IRNAS/smartparks-rhino-tracker-hardware/02_MCU/04_OUTPUT_FILES/Rhino_V2_P1.png

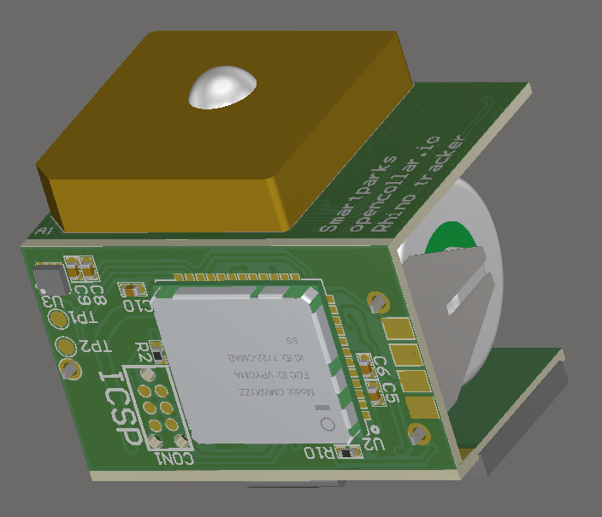
02_MCU/04_OUTPUT_FILES/Rhino_V2_P1.png
