IRNAS/smartparks-rhino-tracker-hardware/11_DOC/Rhino Tracker 3.png

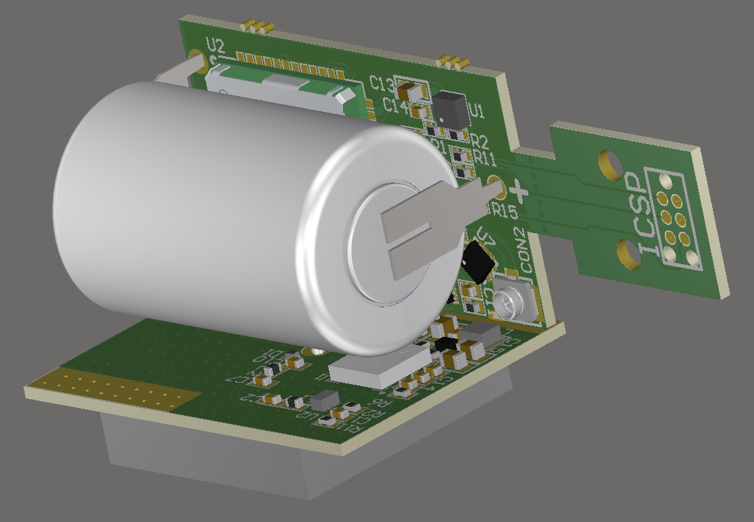
11_DOC/Rhino Tracker 3.png
