IRNAS/smartparks-rhino-tracker-hardware/11_DOC/Rhino_V2_1_3.png

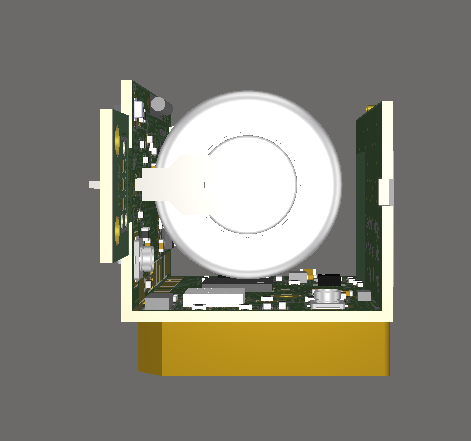
11_DOC/Rhino_V2_1_3.png
