IRNAS/smartparks-rhino-tracker-hardware/02_MCU/06_RELEASE/V2.4/Rhino - MCU_V2.4_3D/Rhino - MCU_V2.4_PCB_3D_PRINT.pdf

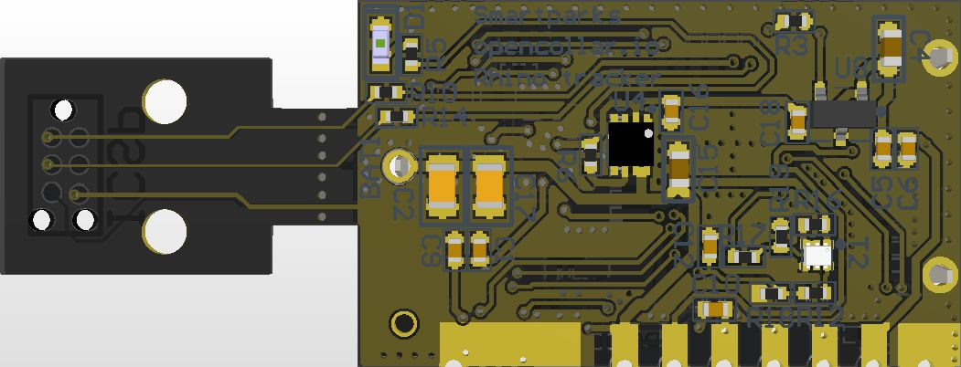
[picture p31: figure]

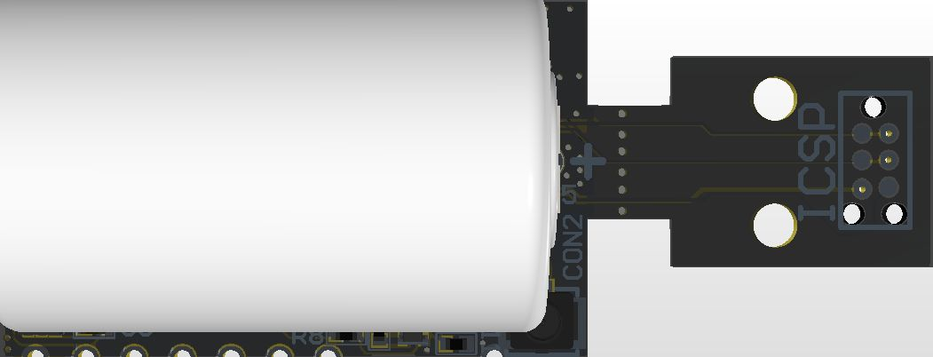
[picture p32: figure]
