IRNAS/smartparks-rhino-tracker-hardware/01_GPS/06_RELEASE/V2.2/Rhino - GPS_V2.2_3D/Rhino - GPS_V2.2_PCB 3D Print.pdf

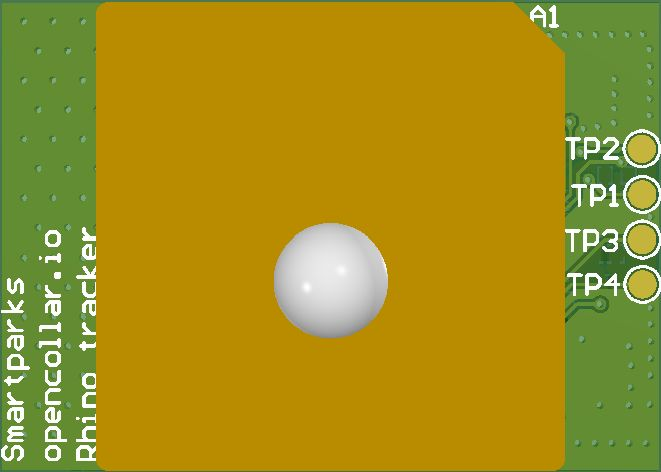
[picture p33: figure]

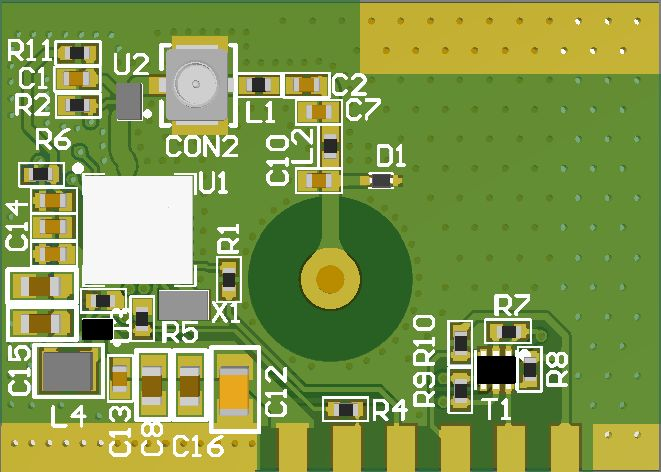
[picture p34: figure]
