IRNAS/smartparks-rhino-tracker-hardware/02_MCU/06_RELEASE/V2.2/Rhino - MCU_V2.2_3D/Rhino - MCU_V2.2_PCB_3D_PRINT.pdf

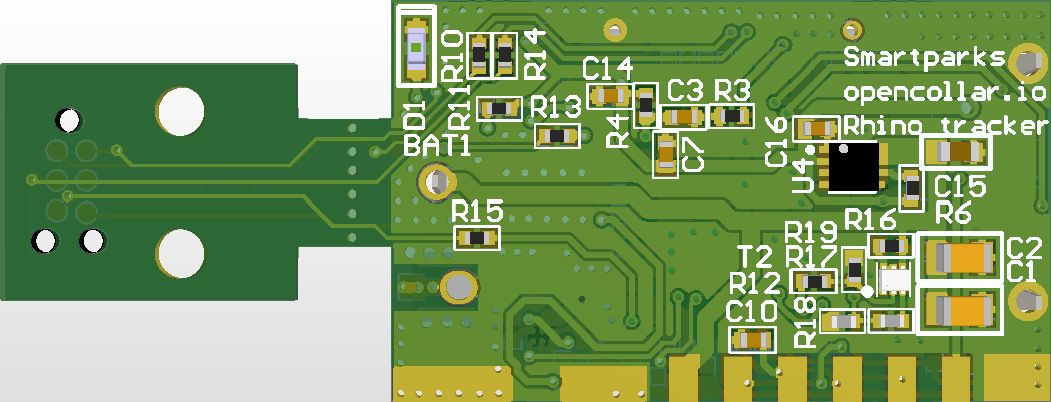
[picture p35: figure]

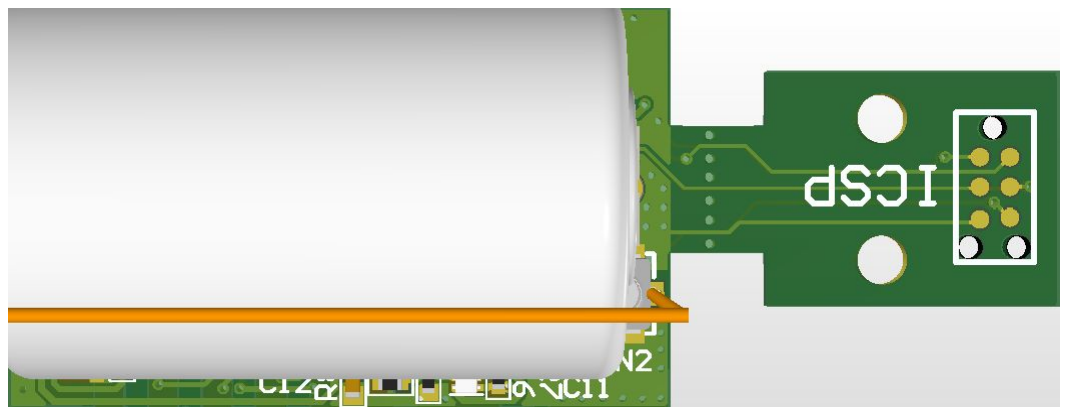
[picture p36: figure]
