IRNAS/smartparks-rhino-tracker-hardware/02_MCU/06_RELEASE/V2.4/Rhino - MCU_V2.4_SCHEMATICS/Rhino - MCU_V2.4_SCHEMATICS.PDF

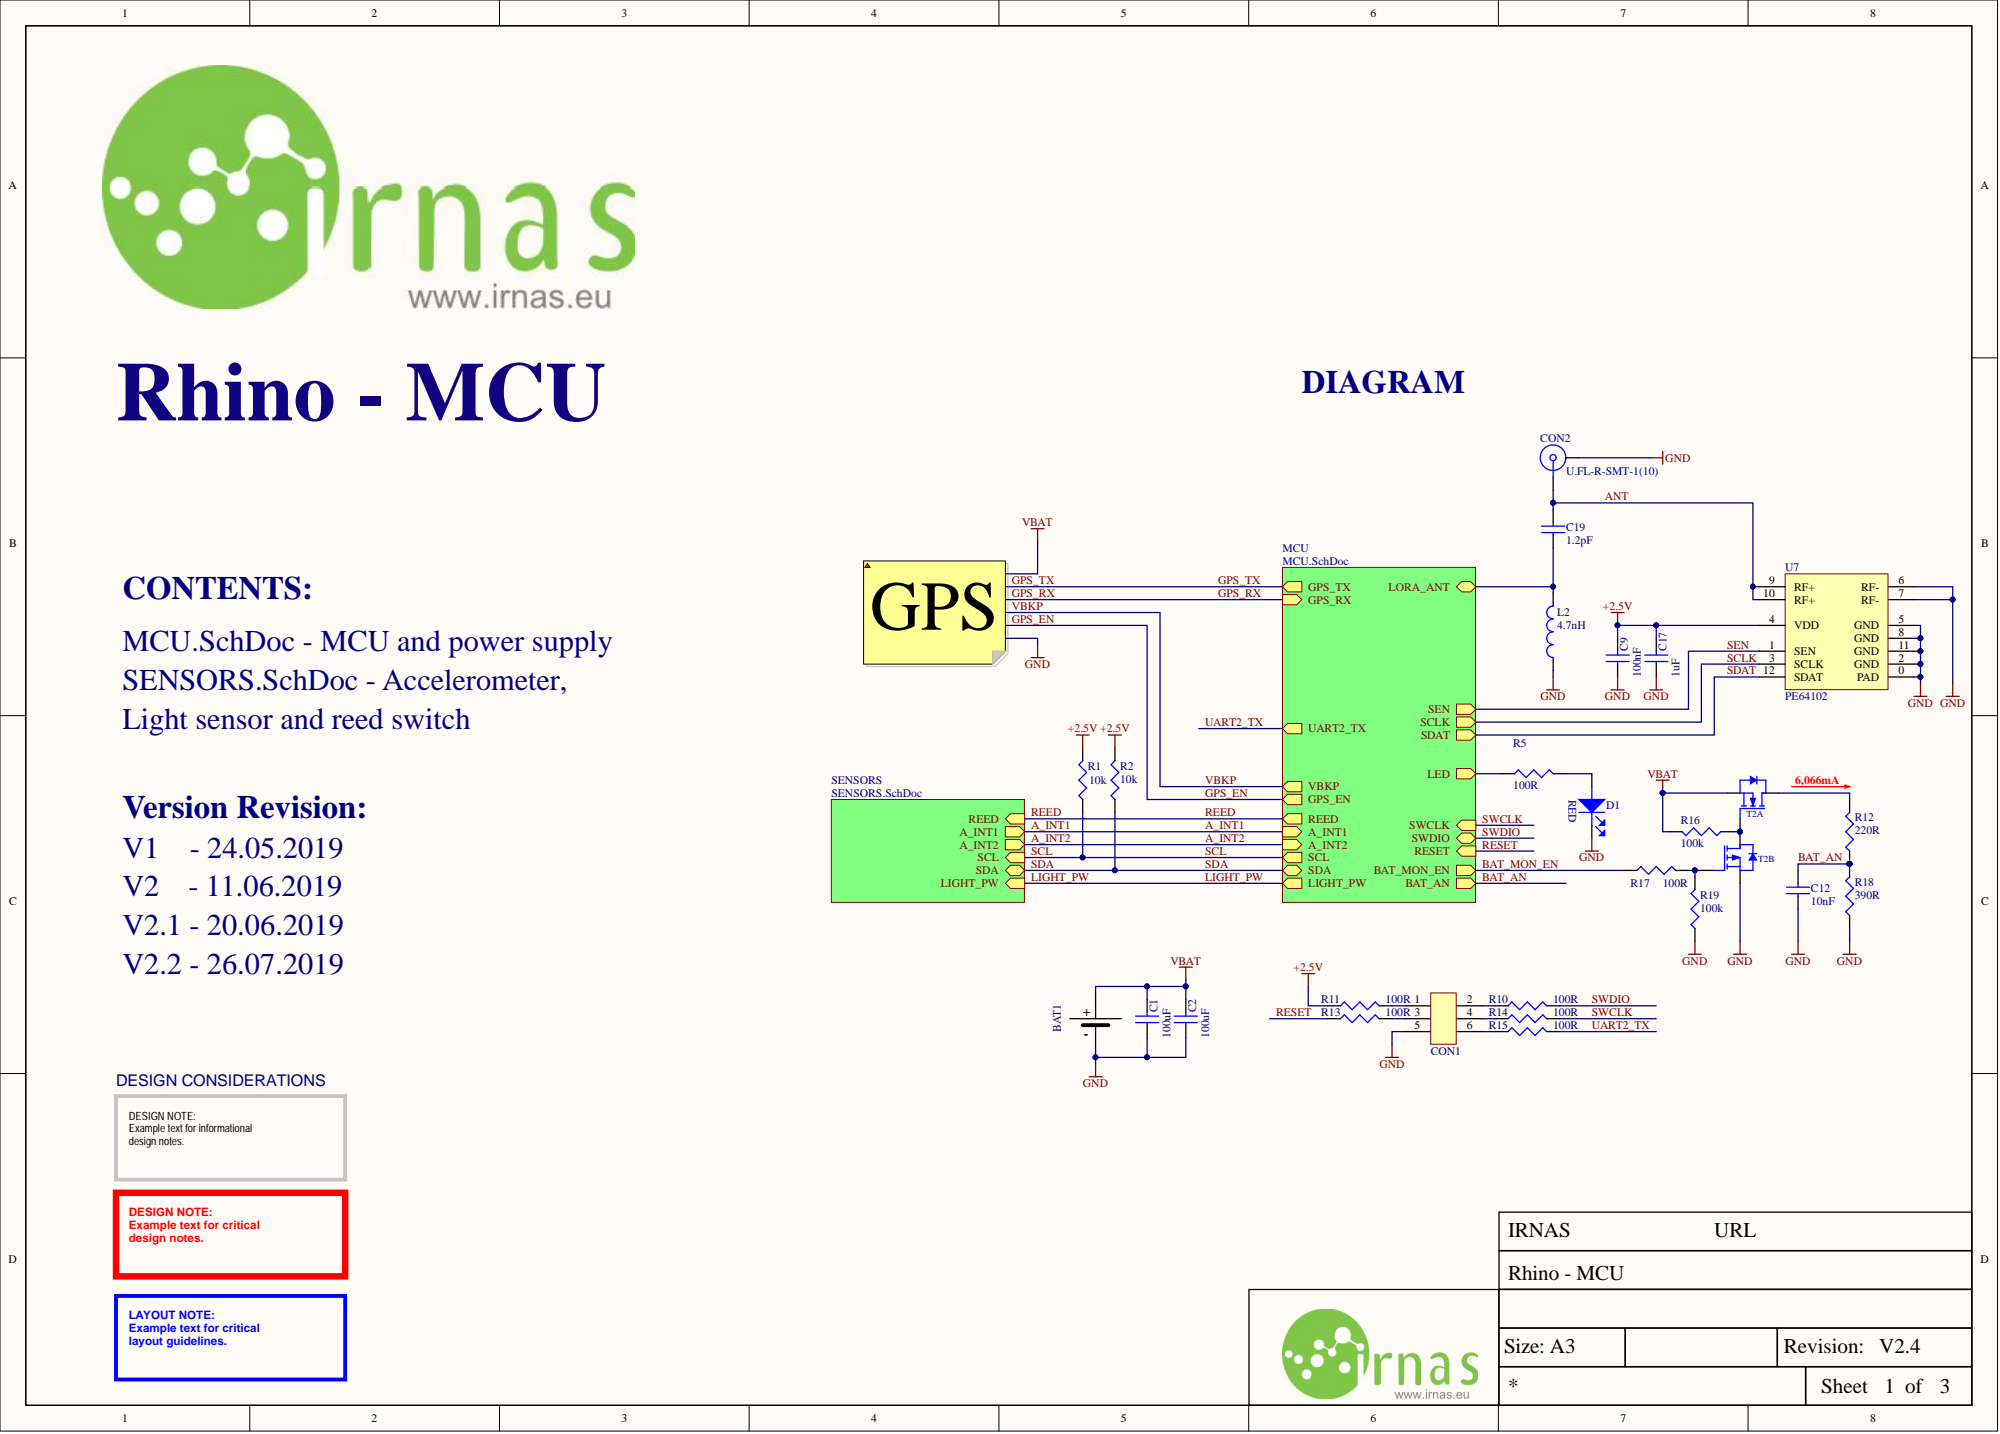
[picture p74: page 1]

MCU.SchDoc - MCU and power supply
SENSORS.SchDoc - Accelerometer,
Light sensor and reed switch

REED A_INT1 A_INT2 SCL SDA LIGHT_PW | REED | REED

A_INT1 | A_INT1
A_INT2 | A_INT2
SCL | SCL
SDA | SDA

DESIGN NOTE:
Example text for informational
design notes.

Example text for critical

LAYOUT NOTE:
layout guidelines.

Size: A3 | | Revision: V2.4

* | Sheet 1 of 3

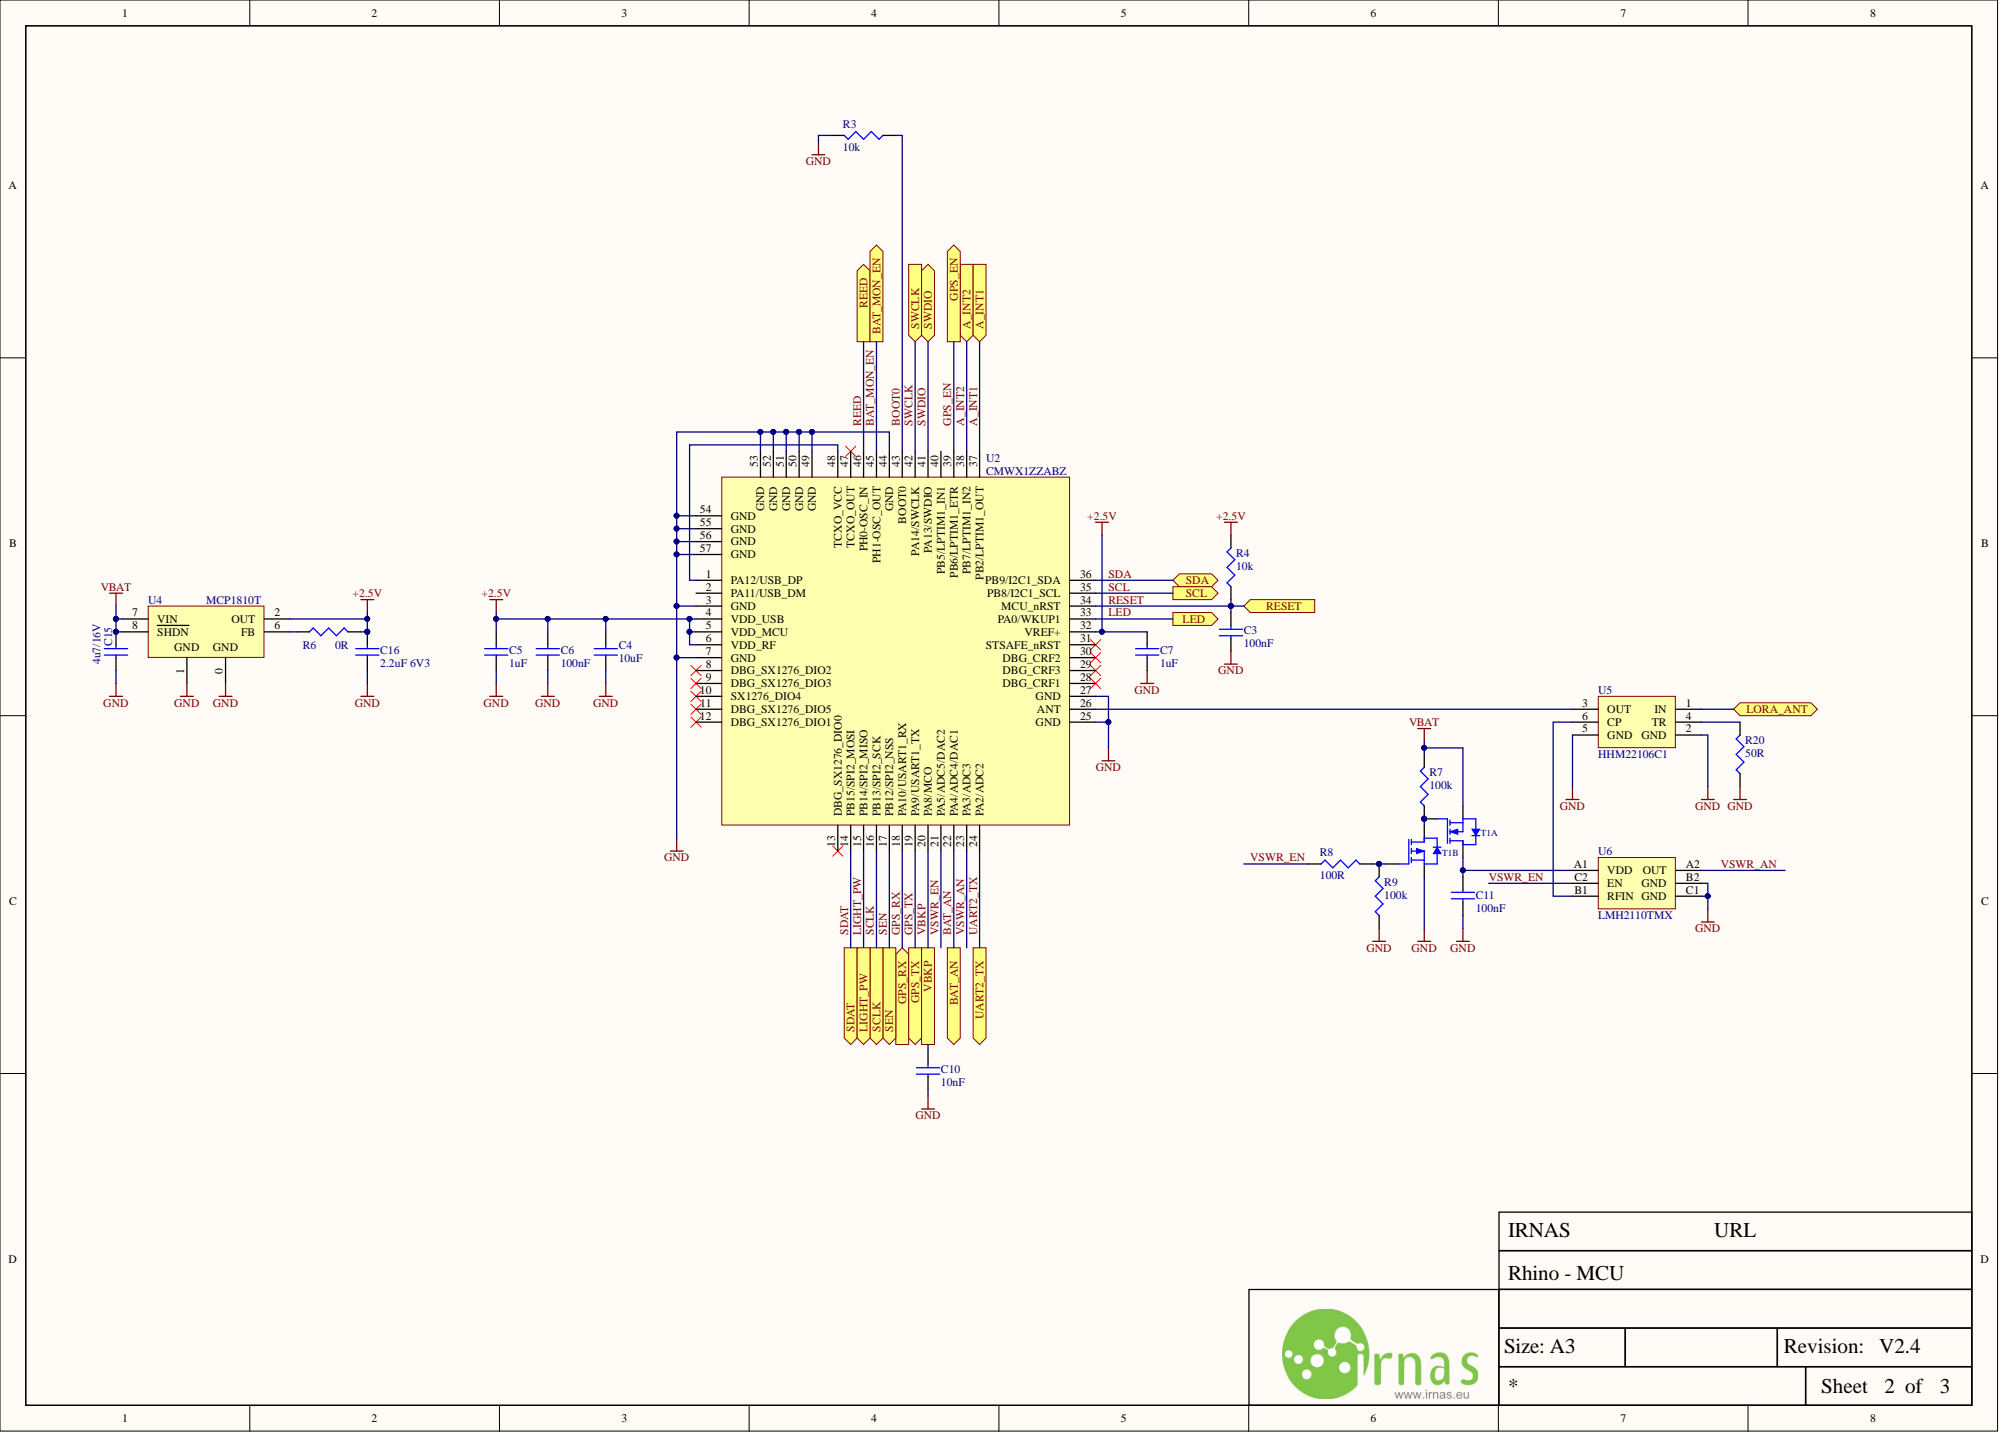
[picture p75: page 2]

GND 50 GND 51 GND 52 GND 53

OUT 37 PB7/LPTIM1_IN2 38 PB6/LPTIM1_ETR 39 PB5/LPTIM1_IN1 40 PA13/SWDIO 41 PA14/SWCLK 42 BOOT0 43 GND 44 PH1-OSC_OUT 45 PH0-OSC_IN 46 TCXO_OUT 47 TCXO_VCC 48

GND 54 | PA0/WKUP1 | 33 MCU_nRST 34 PB8/I2C1_SCL 35 PB9/I2C1_SDA
GND 55
GND 56
GND 57

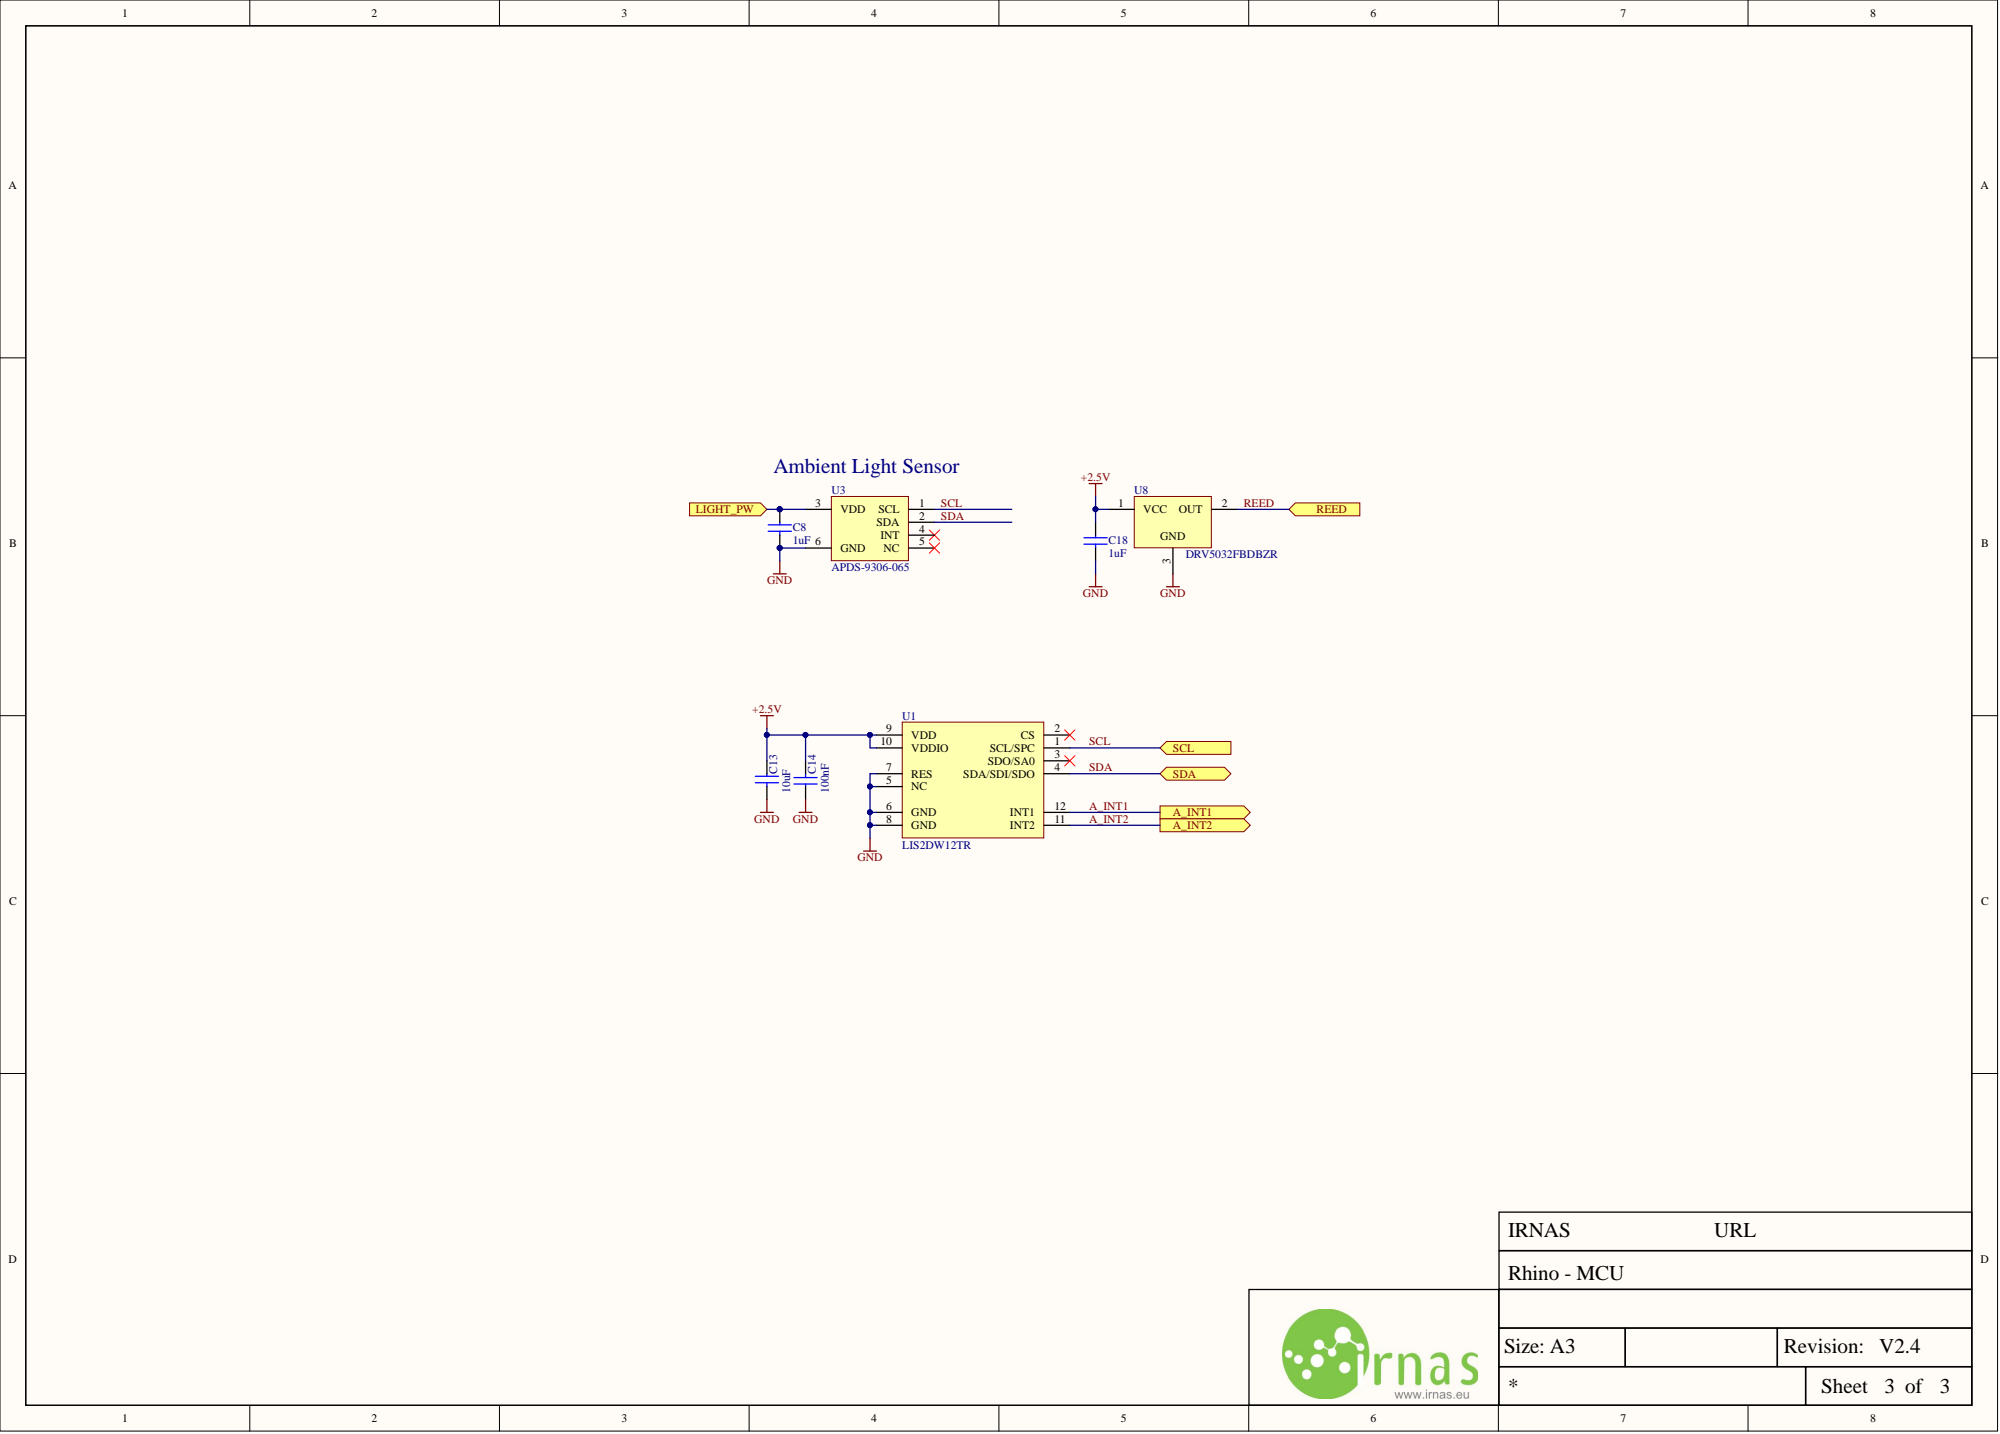
[picture p76: page 3]
