IRNAS/smartparks-rhino-tracker-hardware/01_GPS/06_RELEASE/V2.4/Rhino - GPS_V2.4_Assembly/Rhino - GPS_V2.4_Assembly.PDF

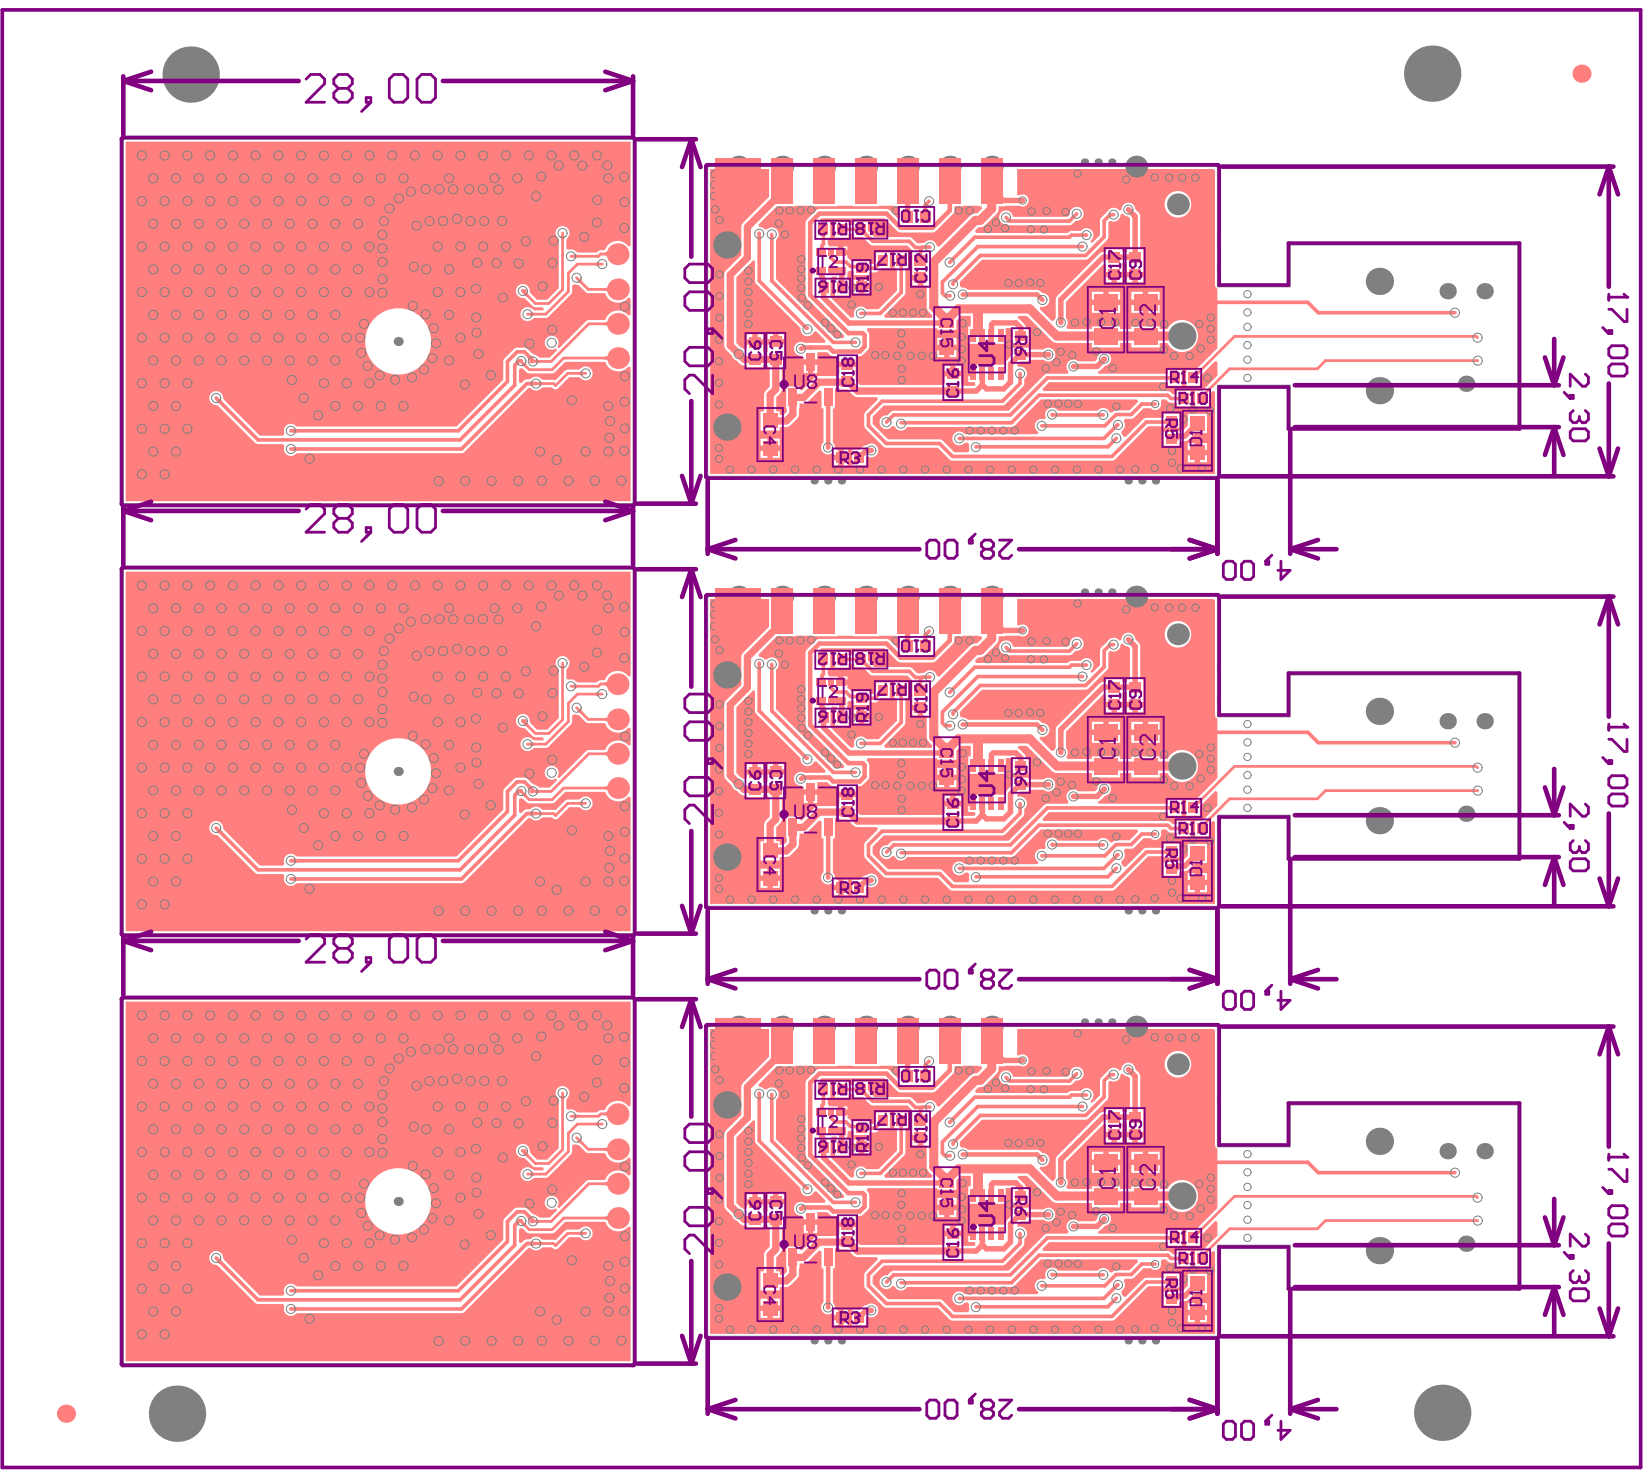
[picture p77: page 1]

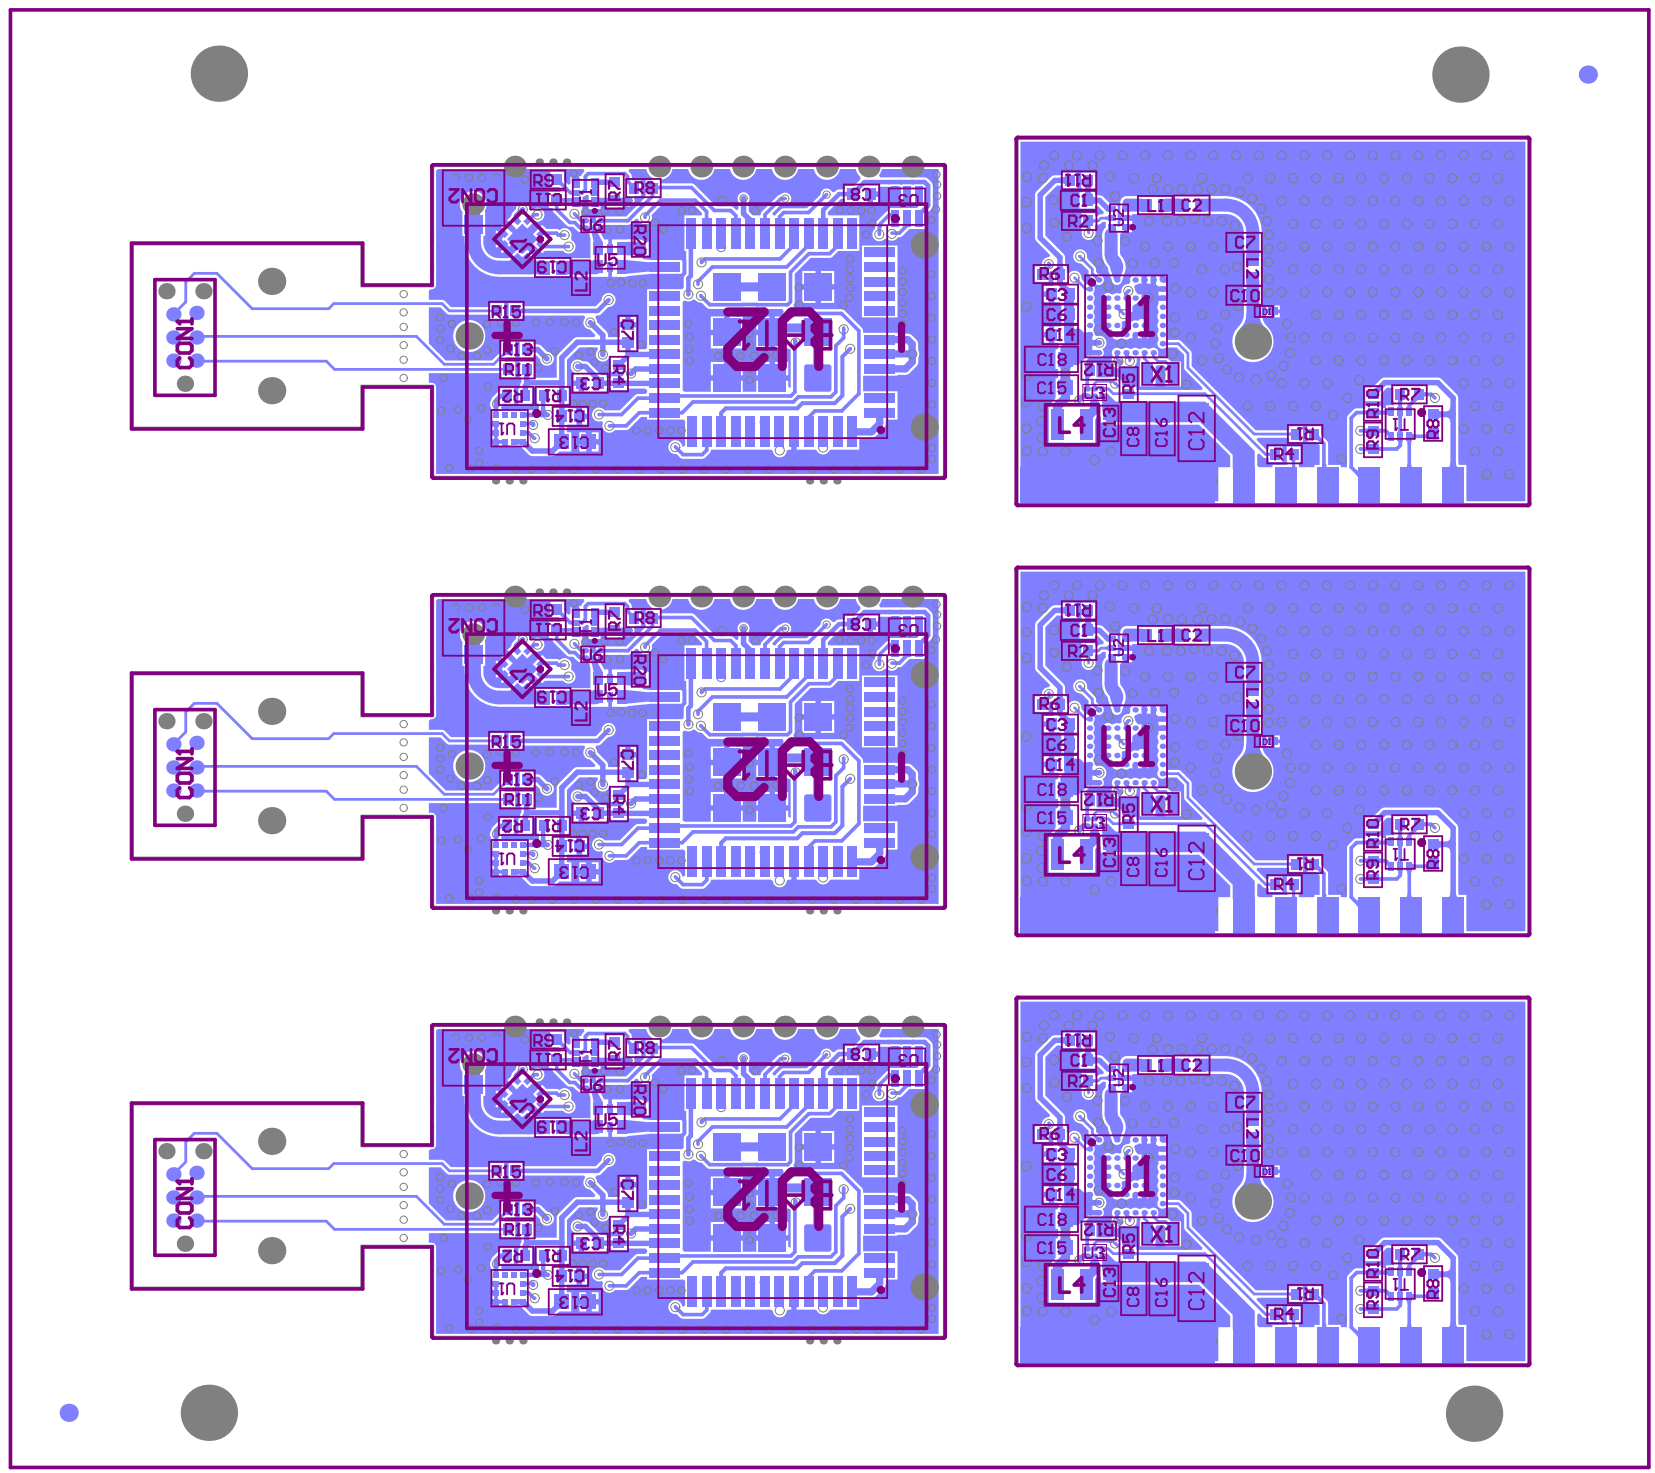
[picture p78: page 2]
