IRNAS/smartparks-rhino-tracker-hardware/01_GPS/06_RELEASE/V2.4/Rhino - GPS_V2.4_PCB_Print/Rhino - GPS_V2.4_PCB_Print.PDF

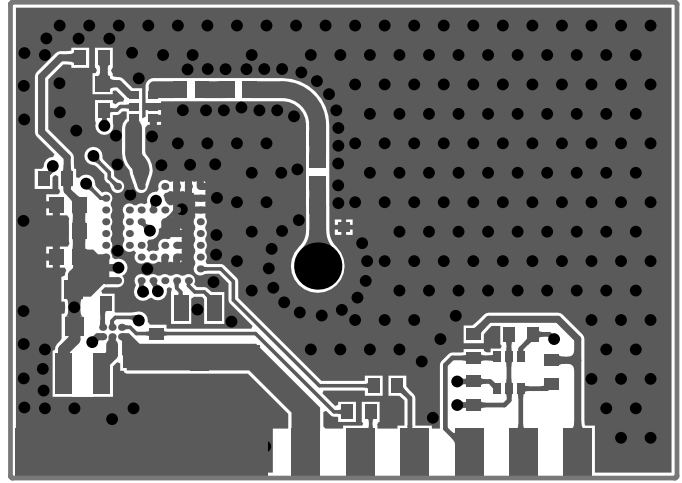
[picture p79: page 4]

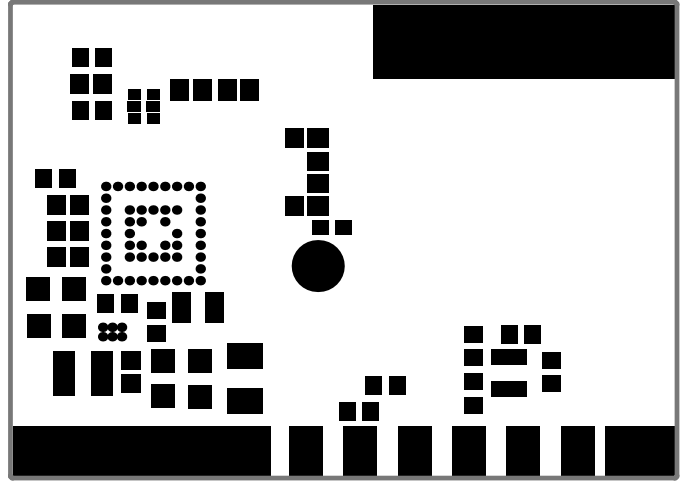
[picture p80: page 5]
