IRNAS/smartparks-rhino-tracker-hardware/02_MCU/06_RELEASE/V2.4/Rhino - MCU_V2.4_PCB_PRINT/Rhino - MCU_V2.4_PCB_PRINT.PDF

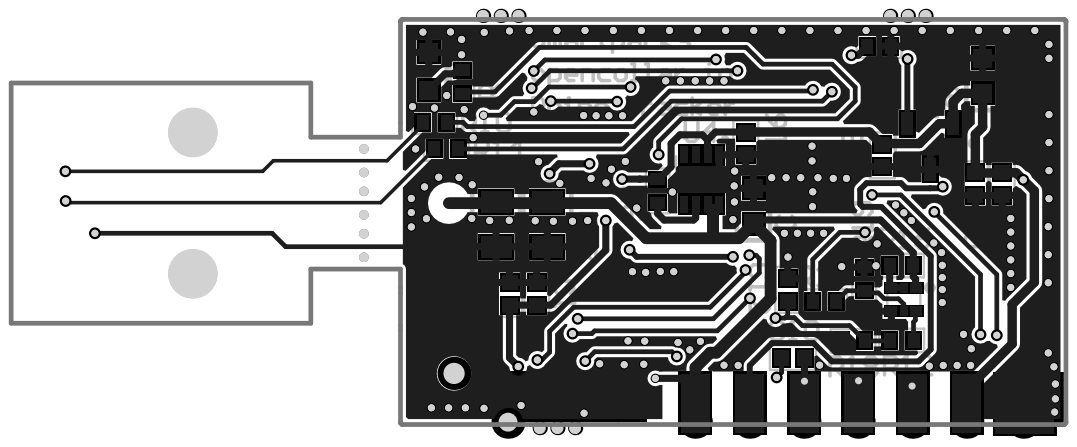
[picture p84: page 1]



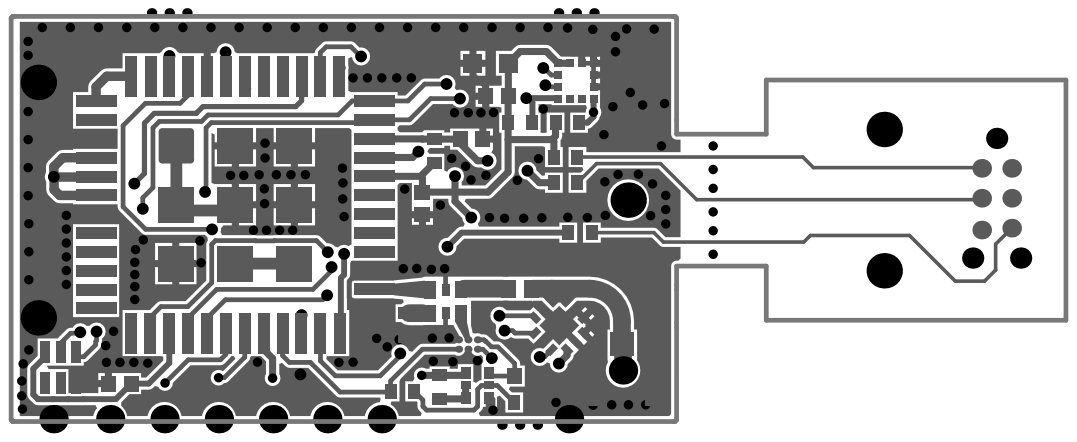
[picture p85: page 4]

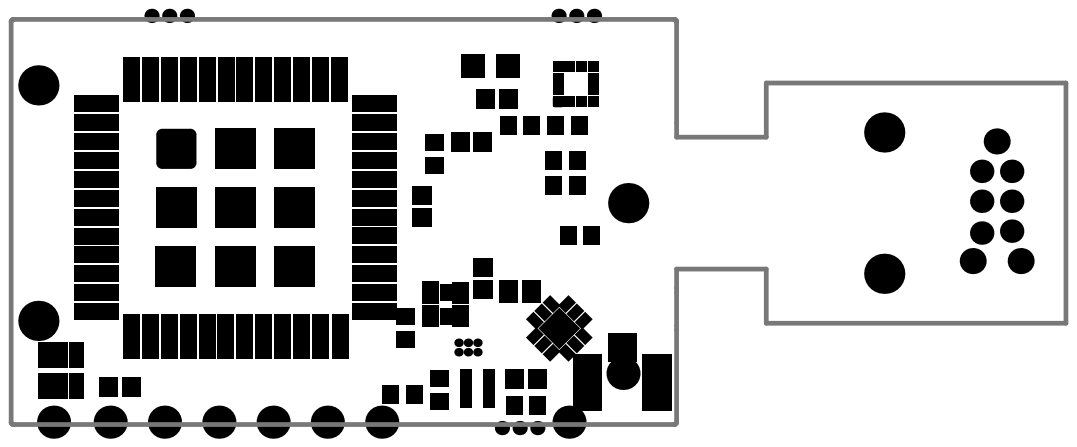
[picture p86: page 5]

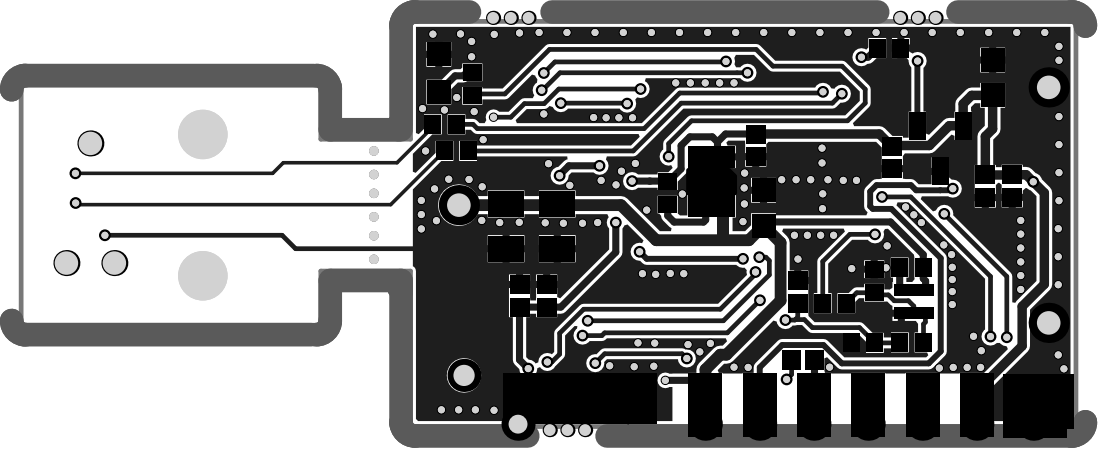
[picture p87: page 6]

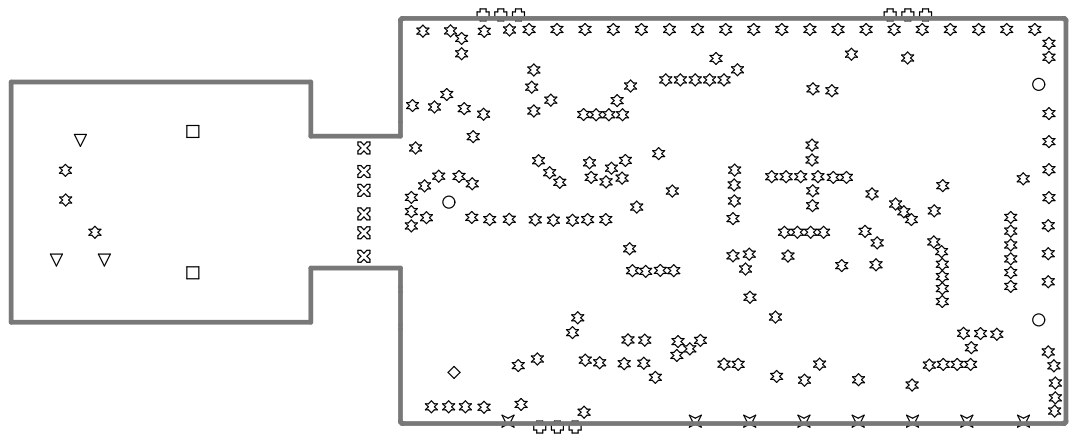
[picture p88: page 7]
