IRNAS/smartparks-rhino-tracker-hardware/01_GPS/06_RELEASE/V2.2/Rhino - GPS_V2.2_Assembly/Rhino - GPS_V2.2_Assembly.PDF

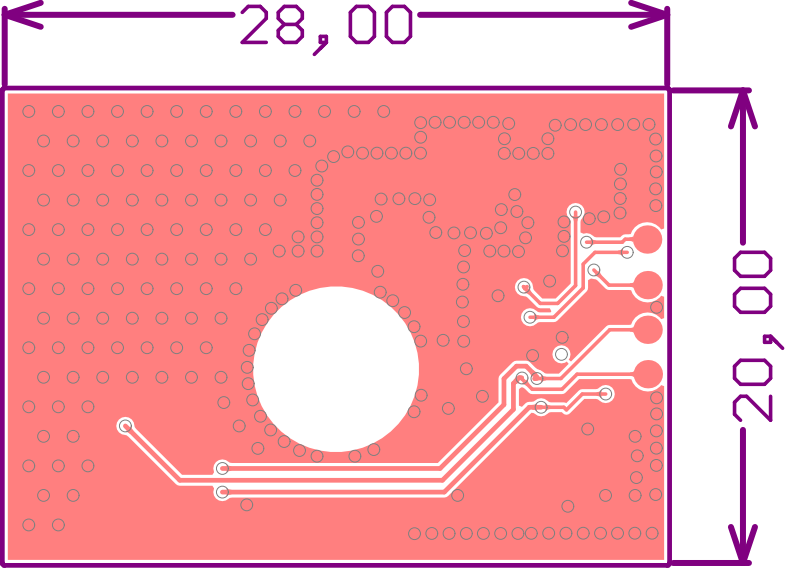
[picture p89: page 1]

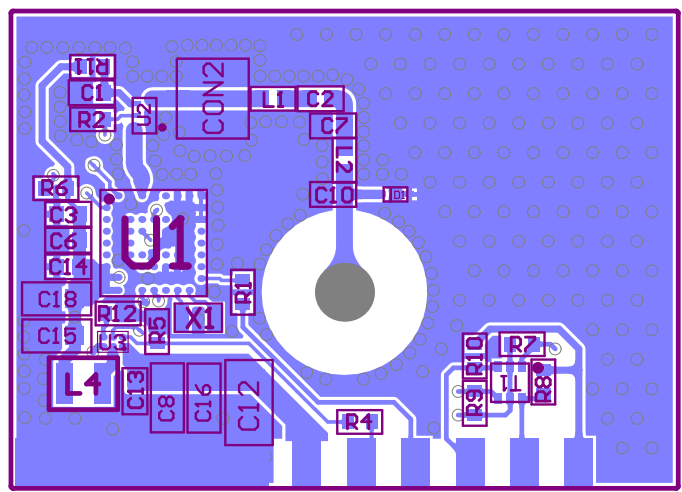
[picture p90: page 2]
