IRNAS/smartparks-rhino-tracker-hardware/01_GPS/06_RELEASE/V2.2/Rhino - GPS_V2.2_PCB_Print/Rhino - GPS_V2.2_PCB_Print.PDF

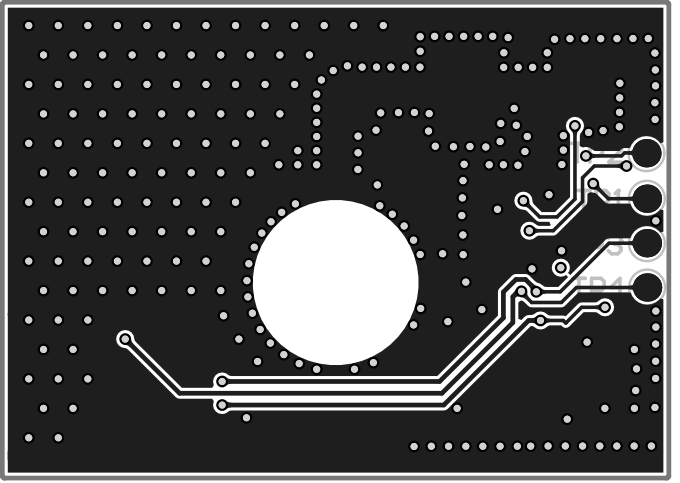
[picture p91: page 1]



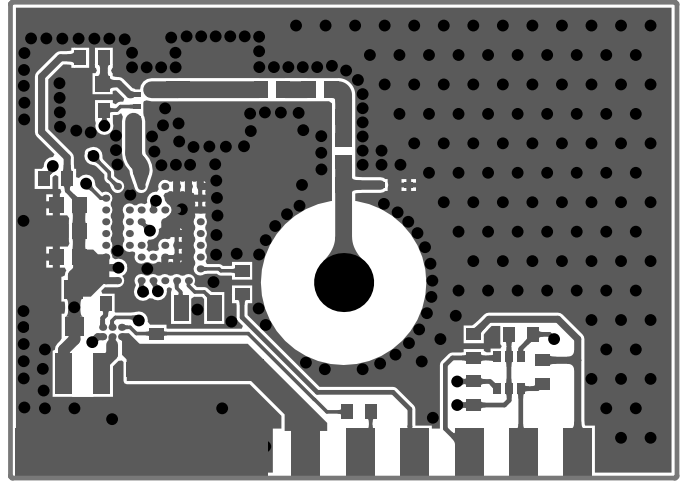
[picture p92: page 4]

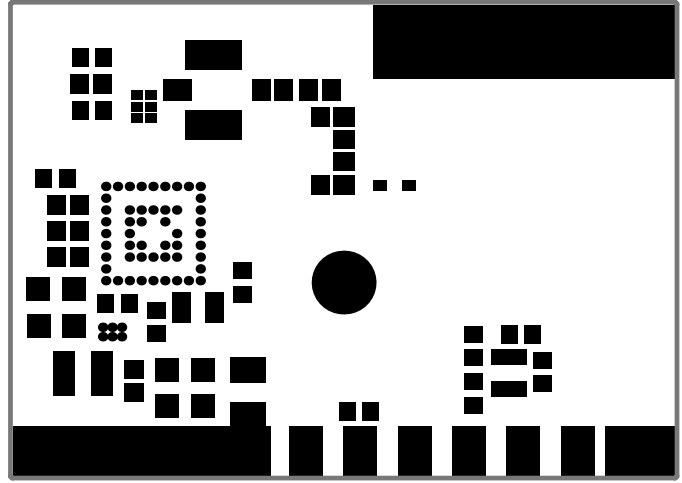
[picture p93: page 5]

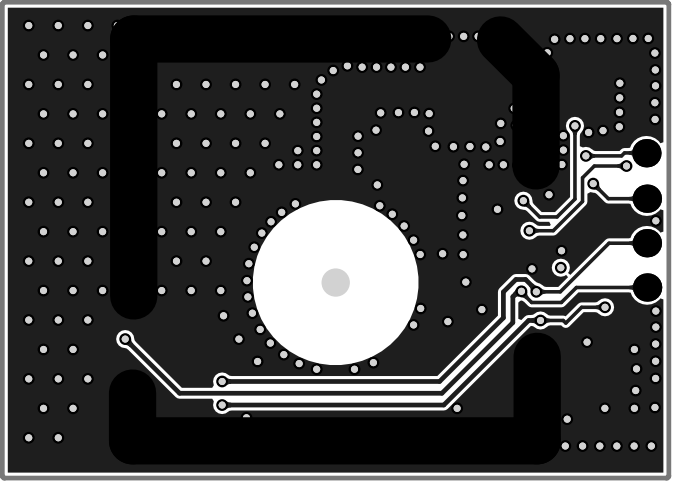
[picture p94: page 6]

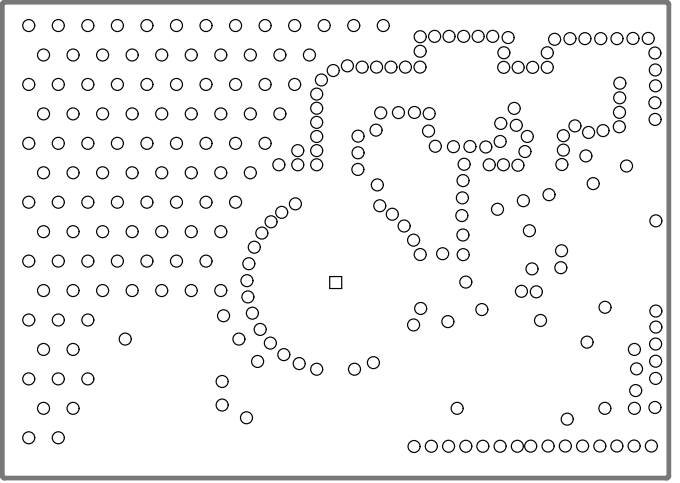
[picture p95: page 7]
