IRNAS/smartparks-rhino-tracker-hardware/01_GPS/06_RELEASE/V2.2/Rhino - GPS_V2.2_SCHEMATICS/Rhino - GPS_V2.2_SCHEMATICS.PDF

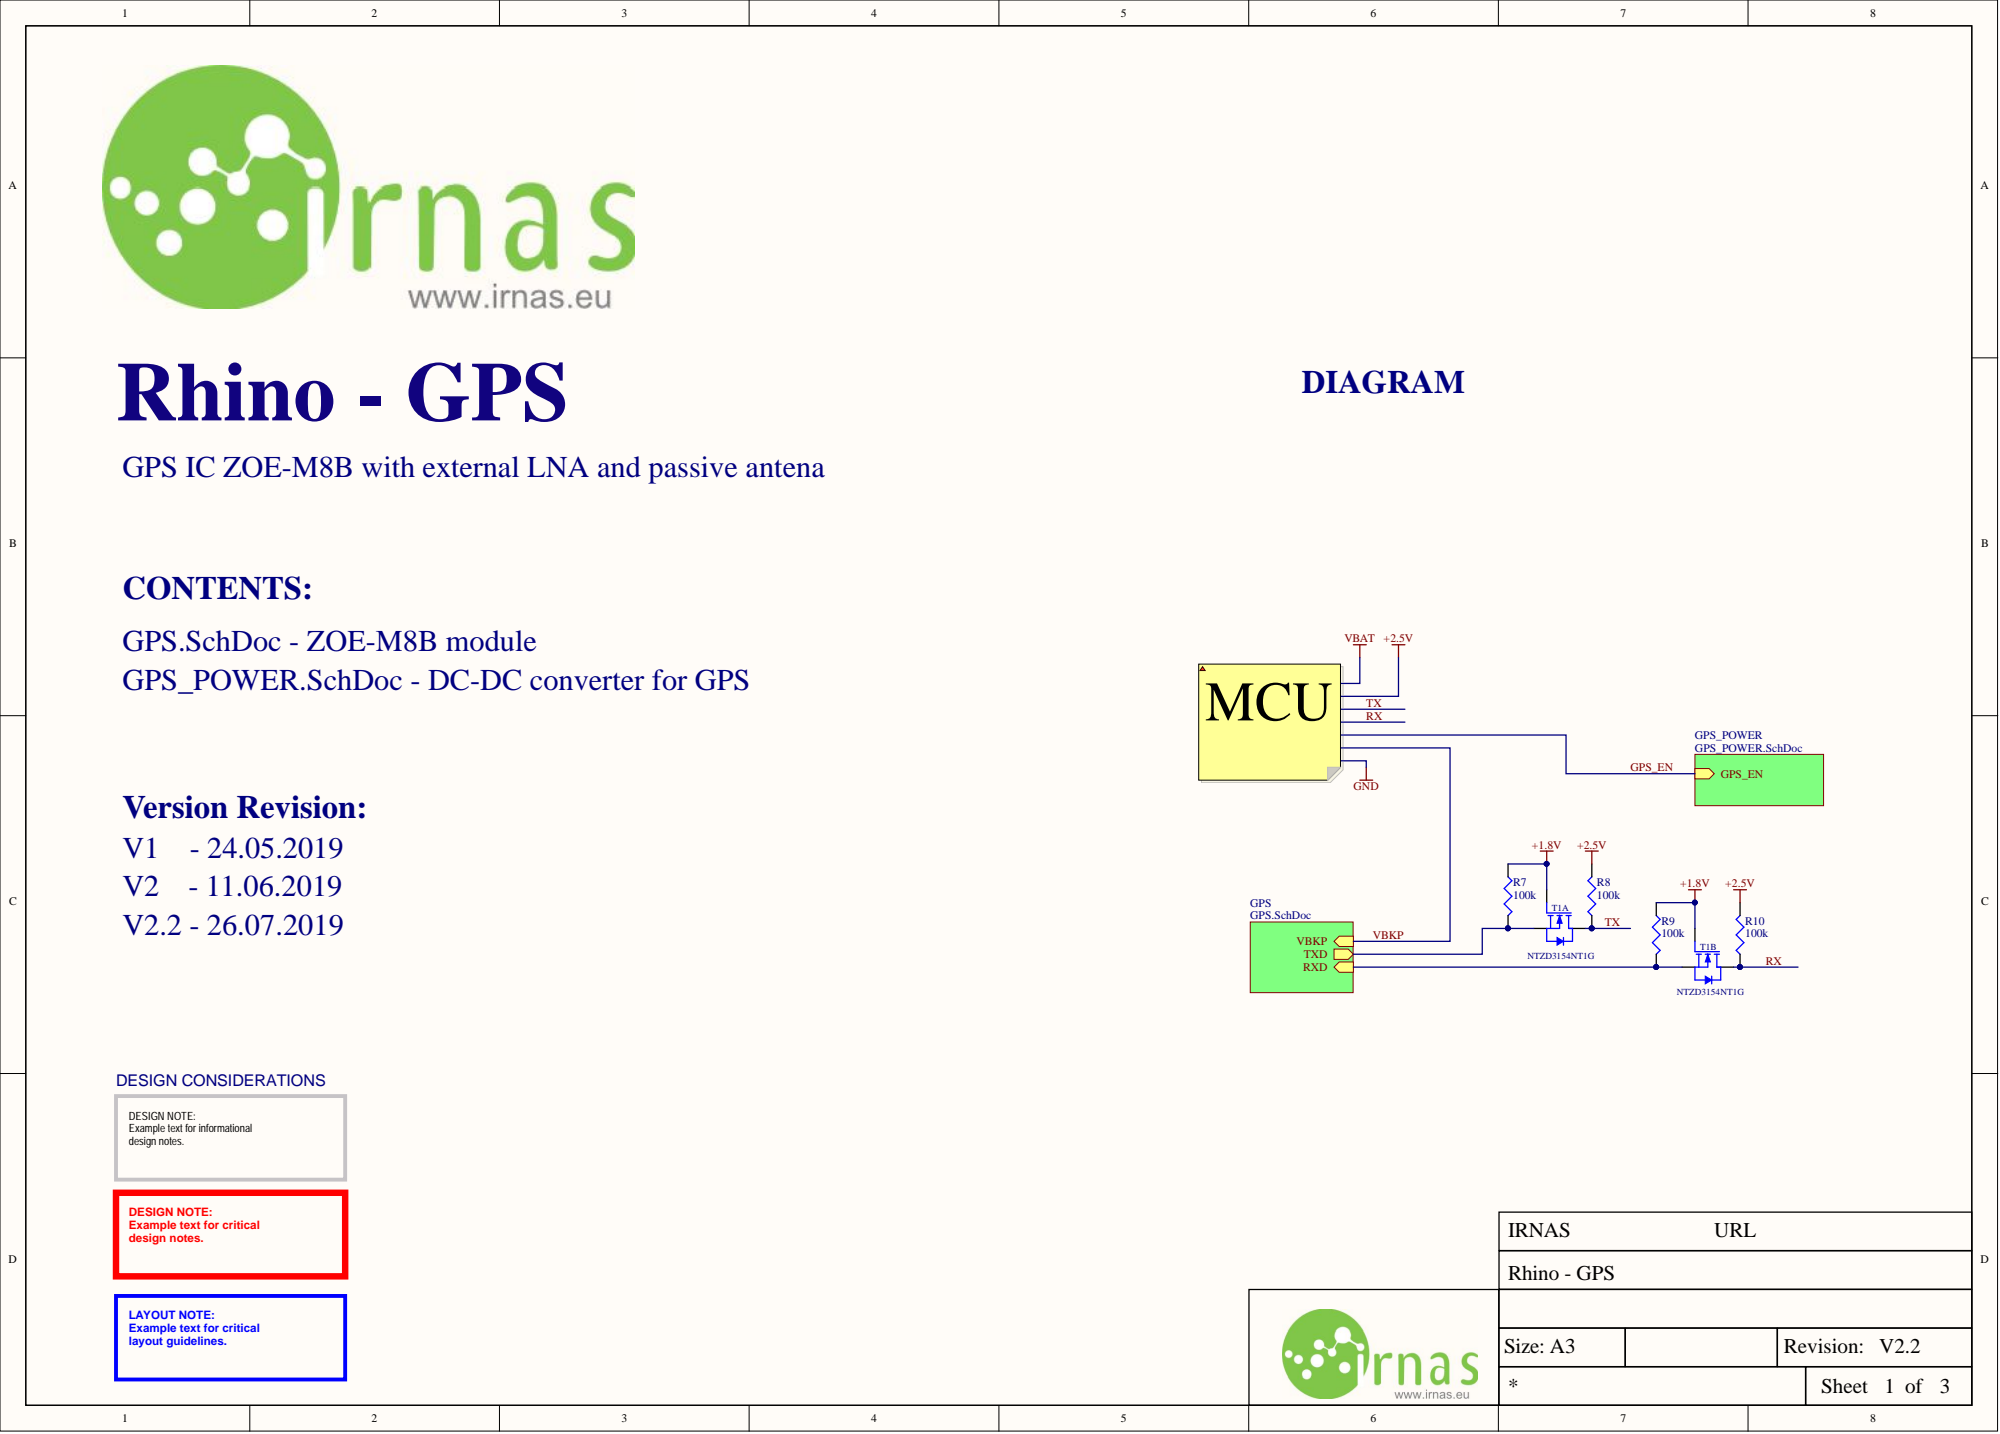
[picture p96: page 1]

GPS IC ZOE-M8B with external LNA and passive antena

GPS.SchDoc - ZOE-M8B module
GPS_POWER.SchDoc - DC-DC converter for GPS

DESIGN NOTE:
Example text for informational
design notes.

Example text for critical

LAYOUT NOTE:
layout guidelines.

Size: A3 | | Revision: V2.2

* | Sheet 1 of 3

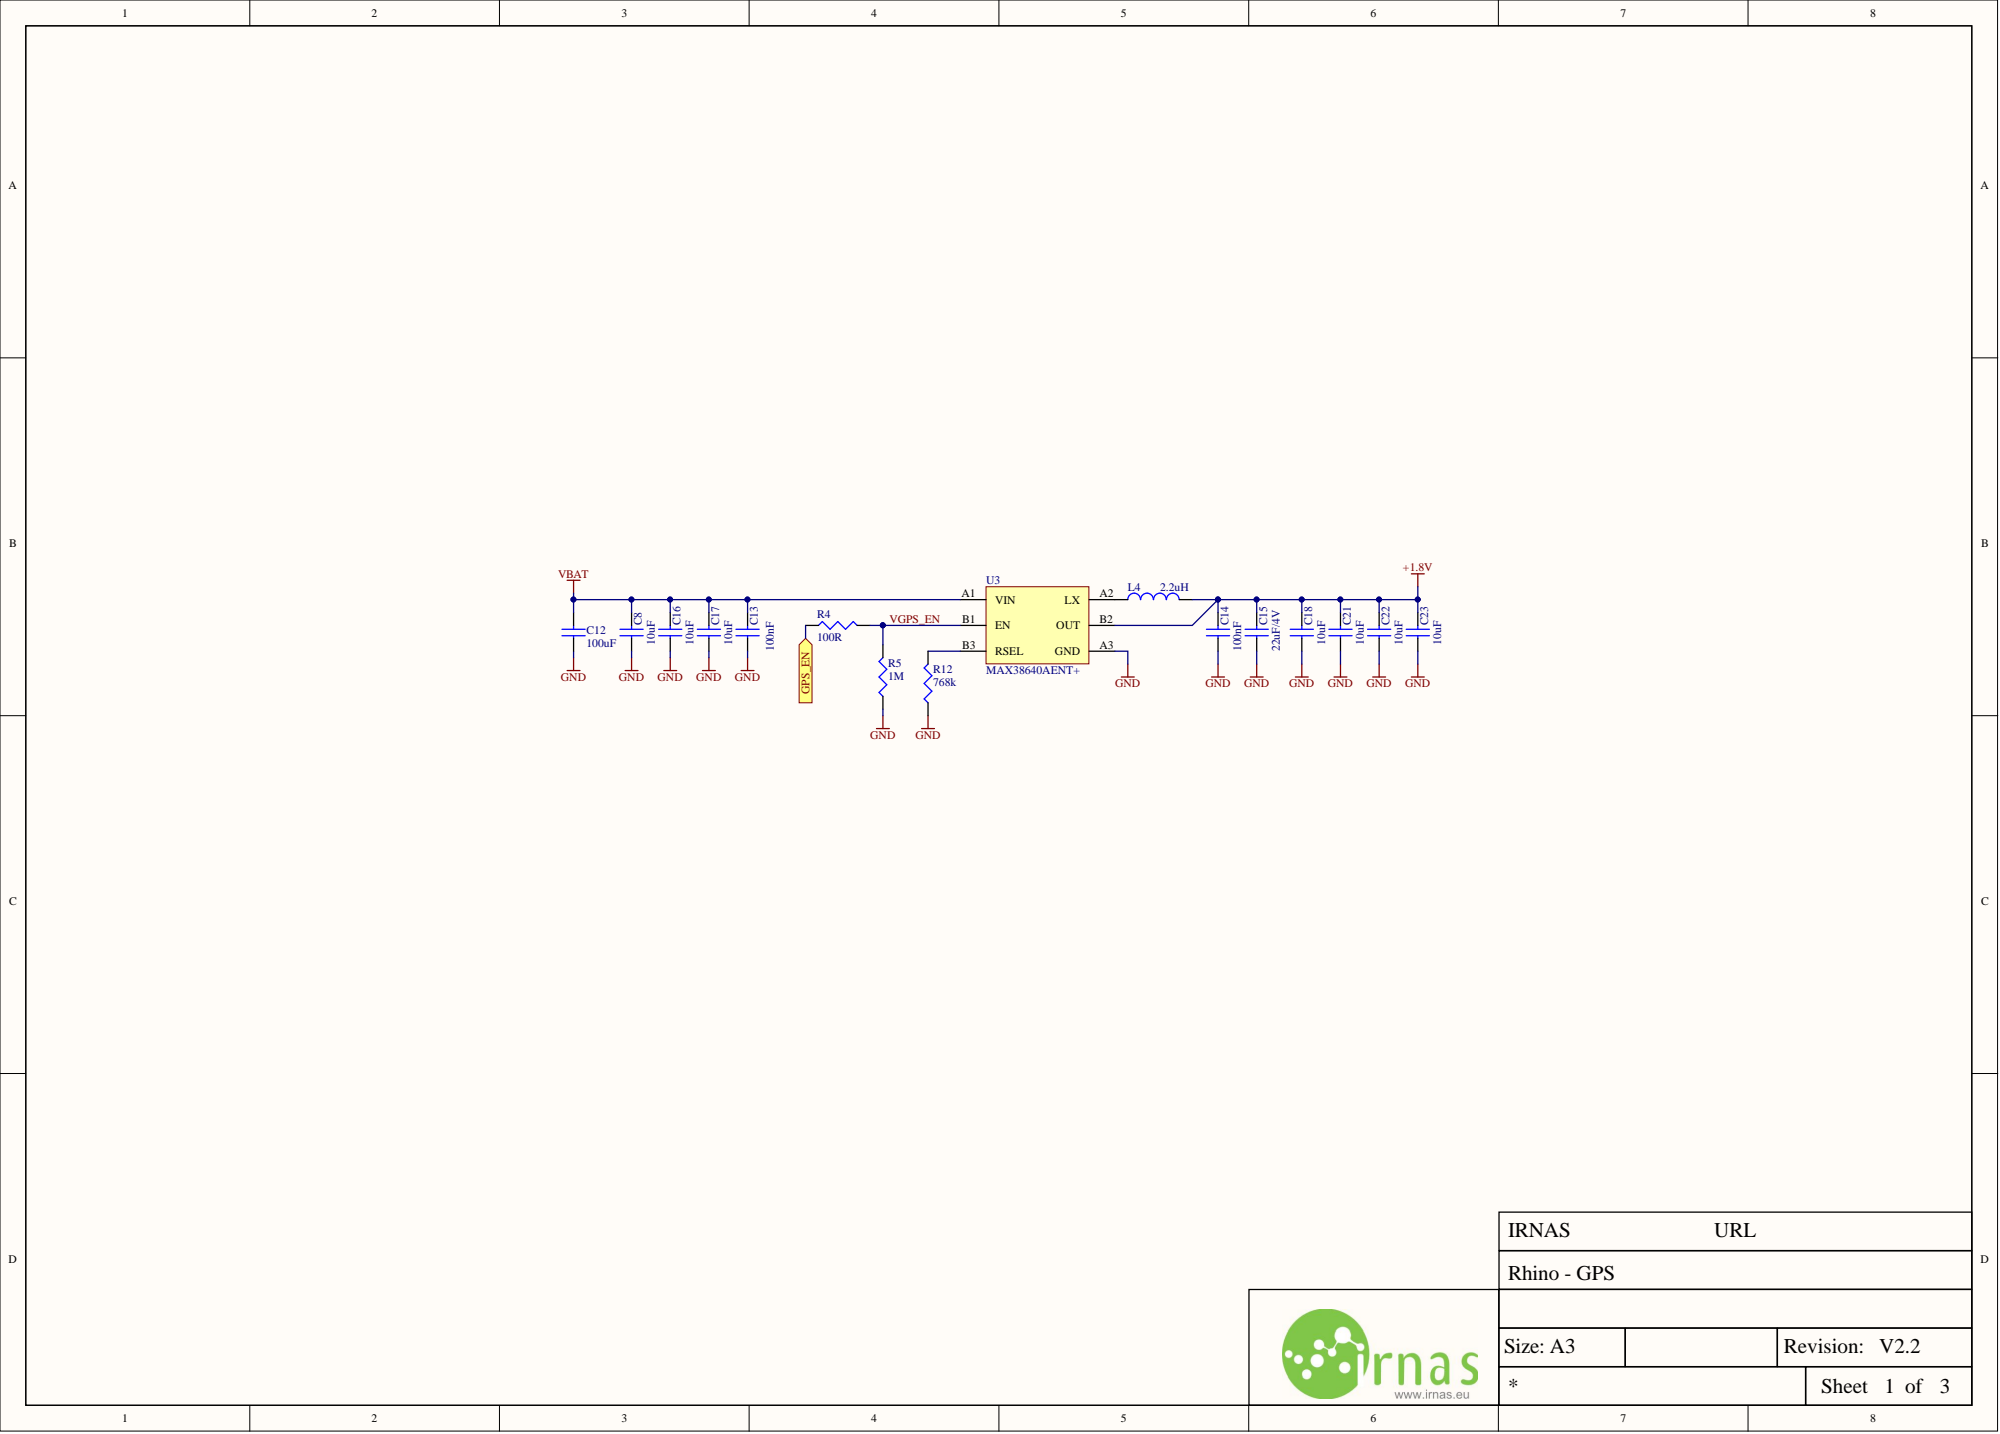
[picture p97: page 2]

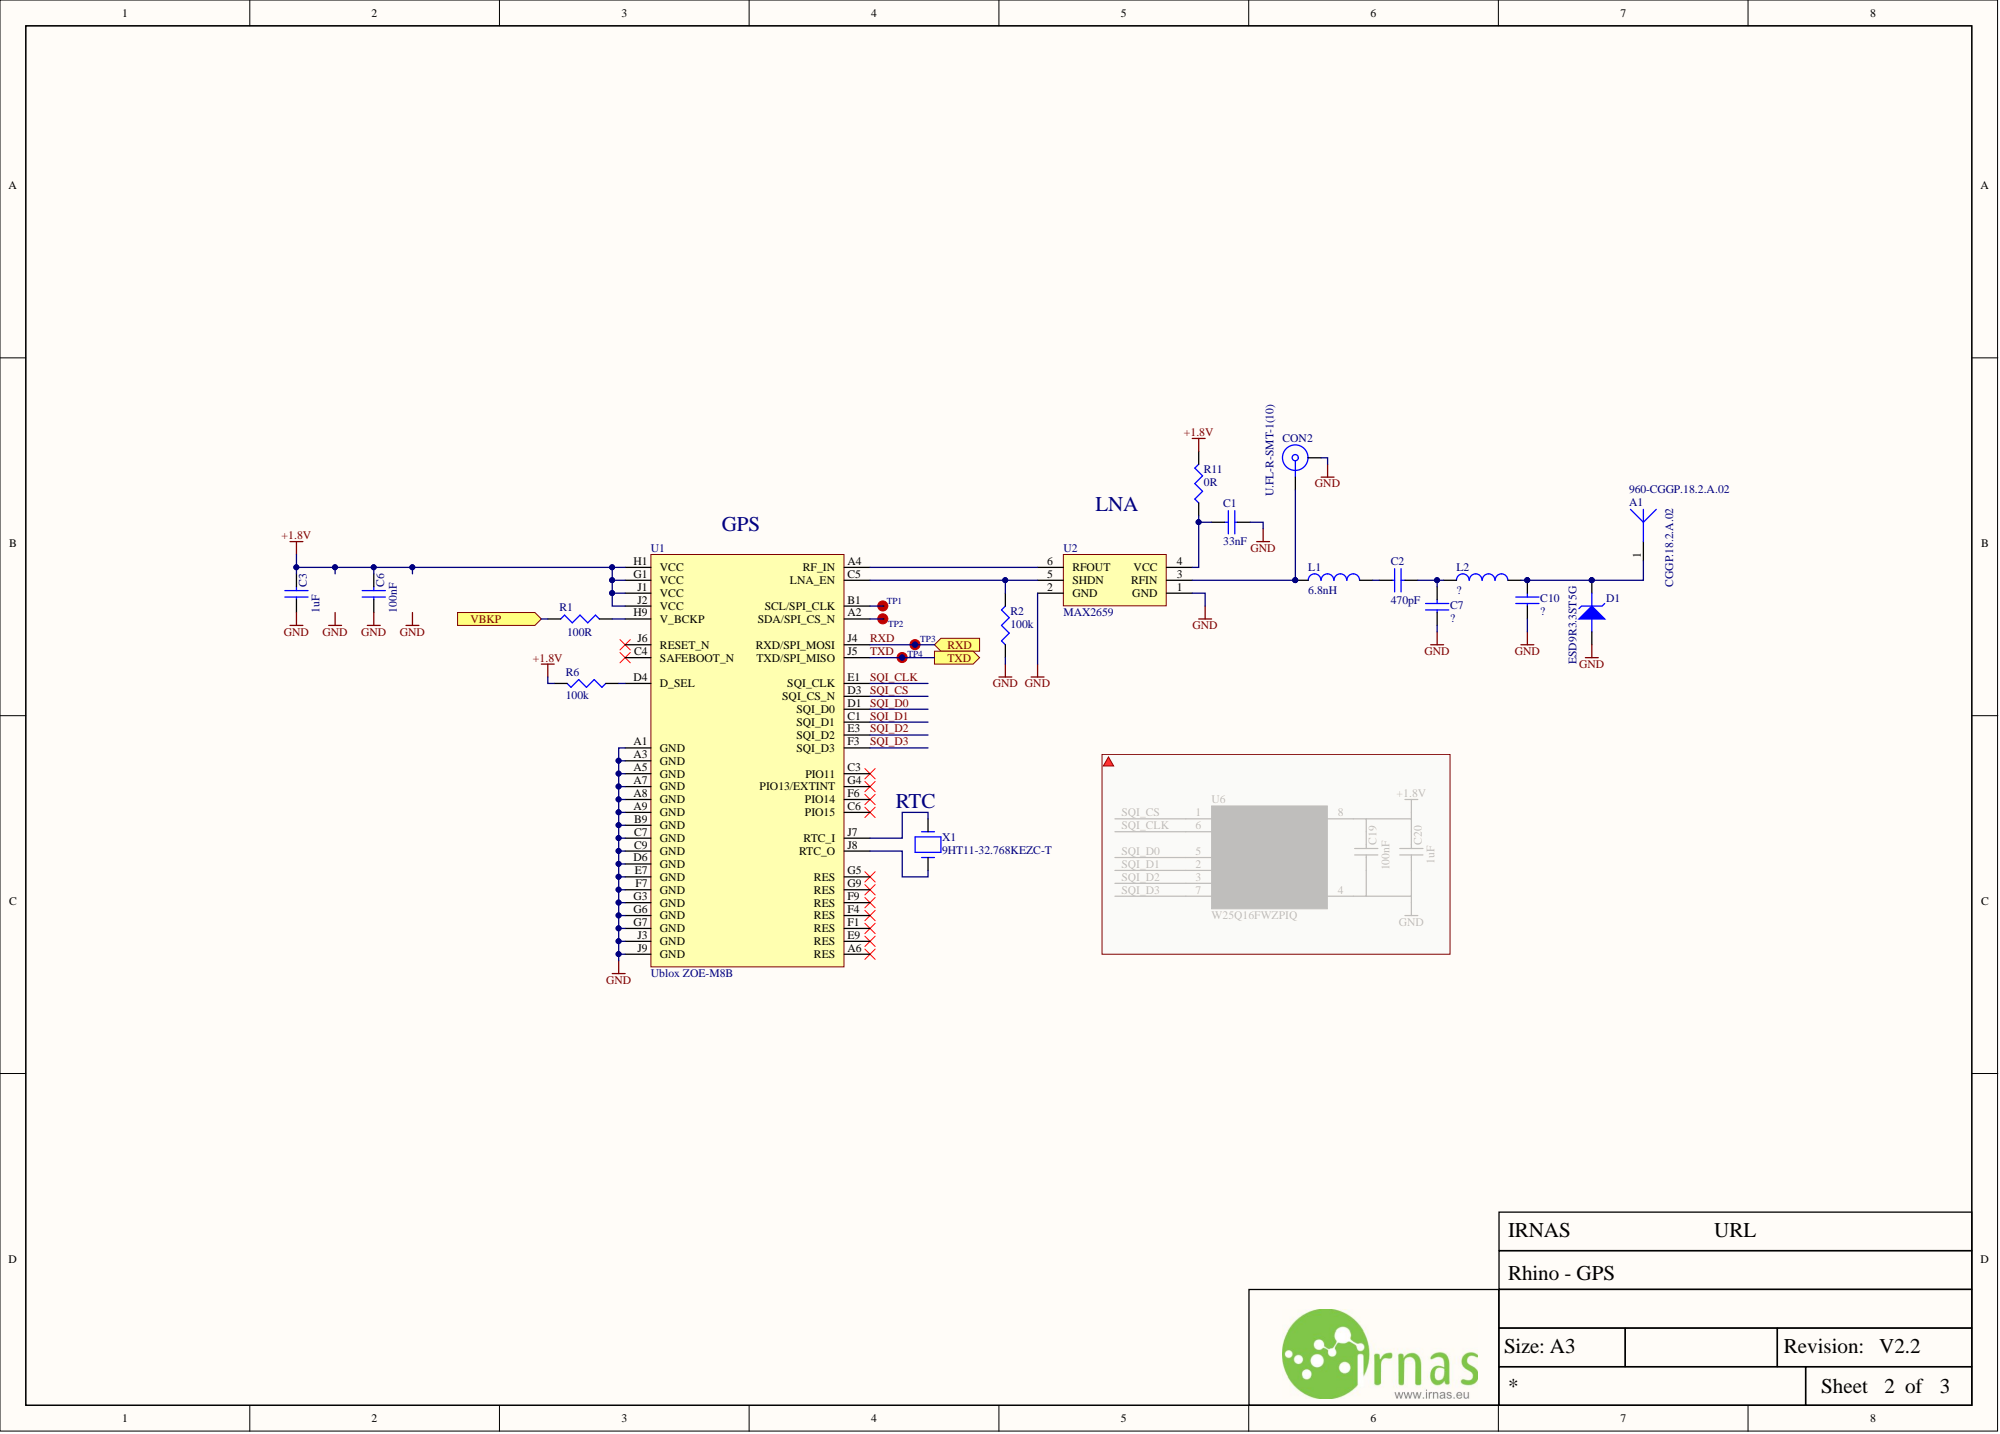
[picture p98: page 3]
