IRNAS/smartparks-rhino-tracker-hardware/02_MCU/06_RELEASE/V2.2/Rhino - MCU_V2.2_ASSEMBLY/Rhino - MCU_V2.2_ASSEMBLY.PDF

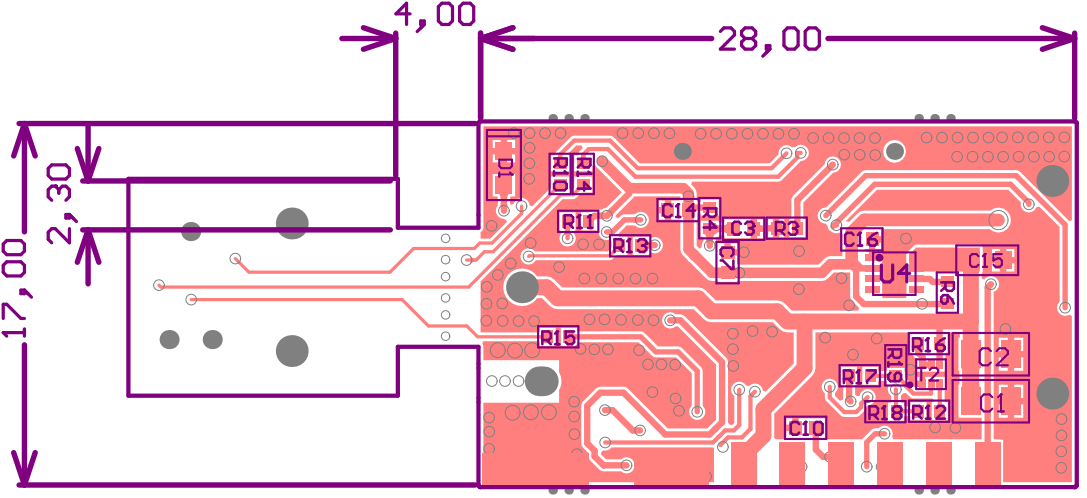
[picture p99: page 1]

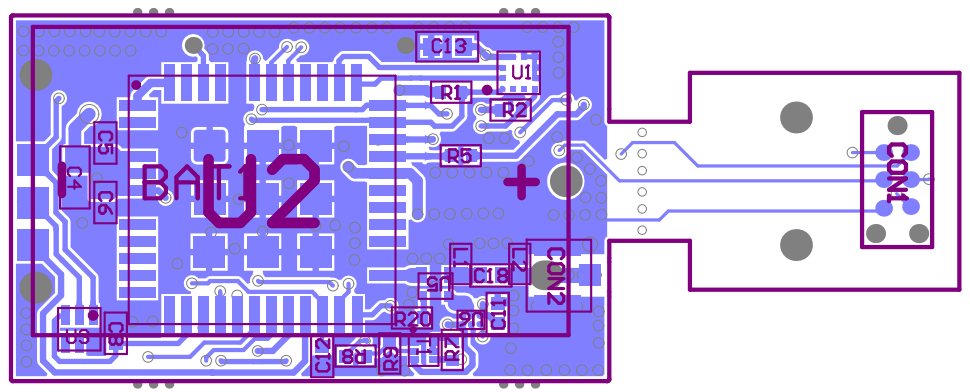
[picture p100: page 2]
