IRNAS/smartparks-rhino-tracker-hardware/02_MCU/06_RELEASE/V2.2/Rhino - MCU_V2.2_PCB_PRINT/Rhino - MCU_V2.2_PCB_PRINT.PDF

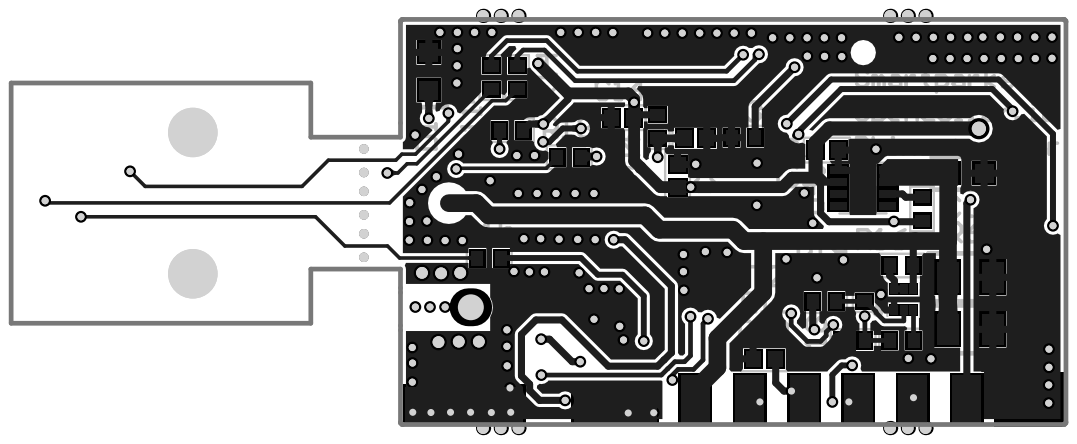
[picture p101: page 1]



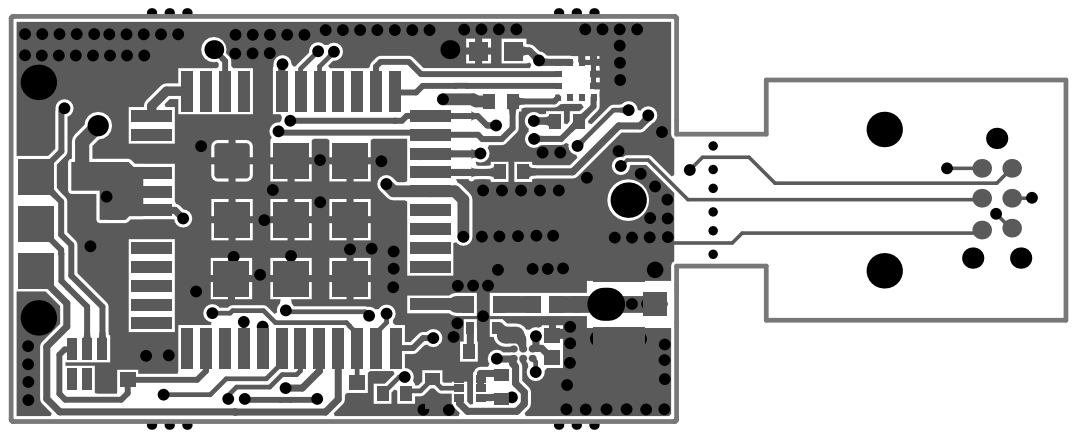
[picture p102: page 4]

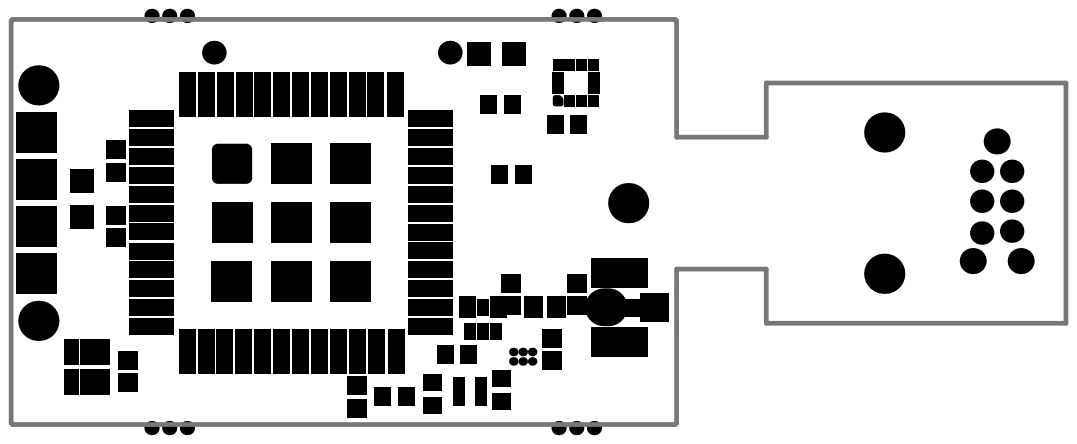
[picture p103: page 5]

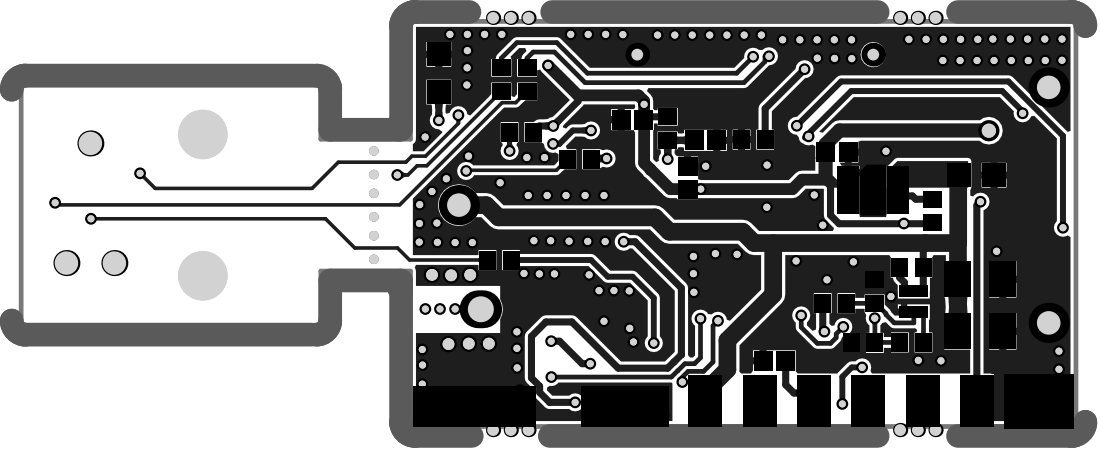
[picture p104: page 6]

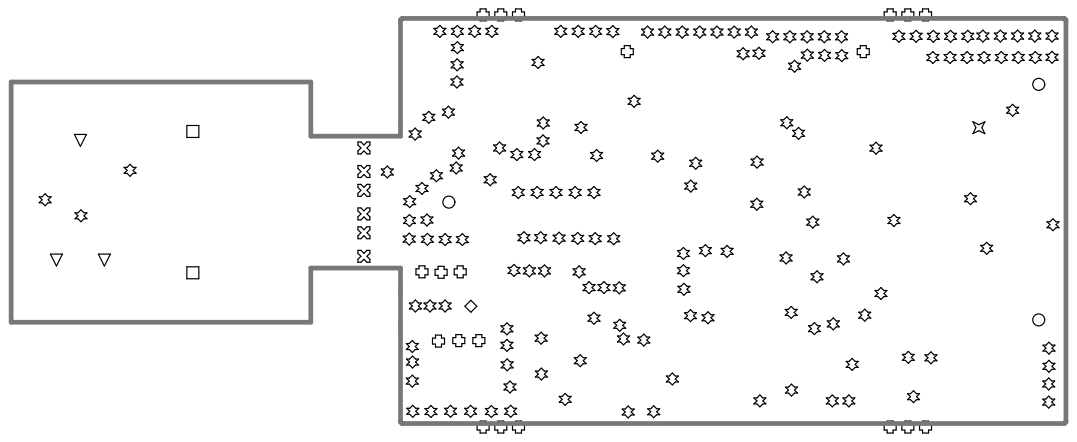
[picture p105: page 7]
