IRNAS/smartparks-rhino-tracker-hardware/03_LORA_ANT/06_RELEASE/V1.0/Rhino - LORA ANT_V1_Assembly/Rhino - LORA ANT_V1_Assembly.PDF

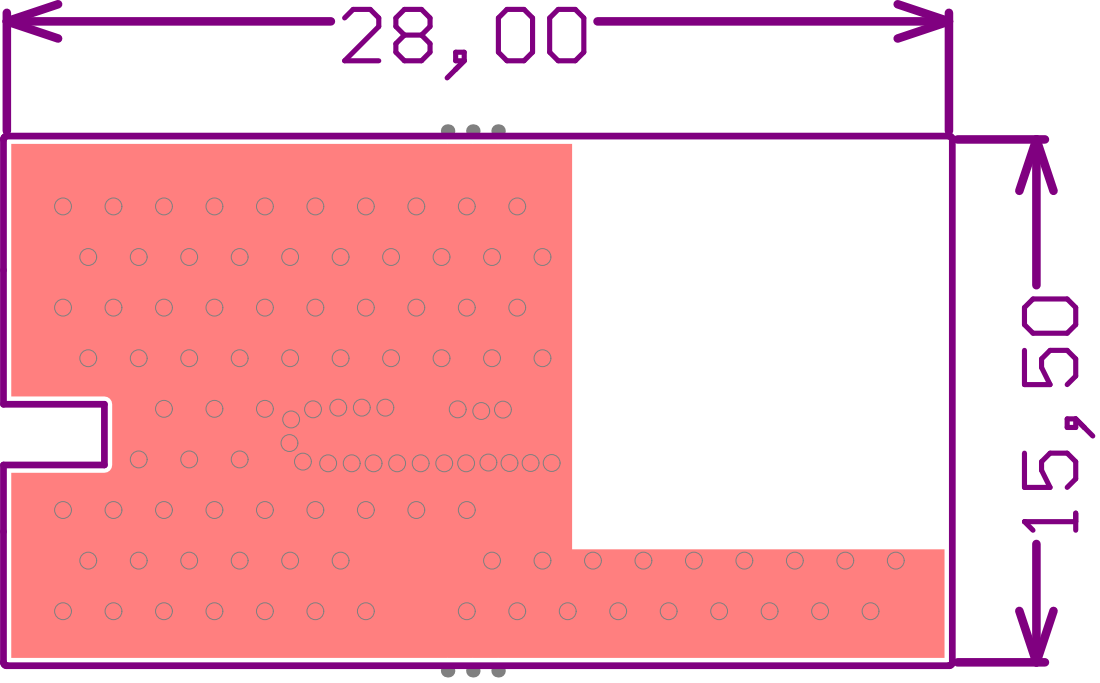
[picture p106: page 1]

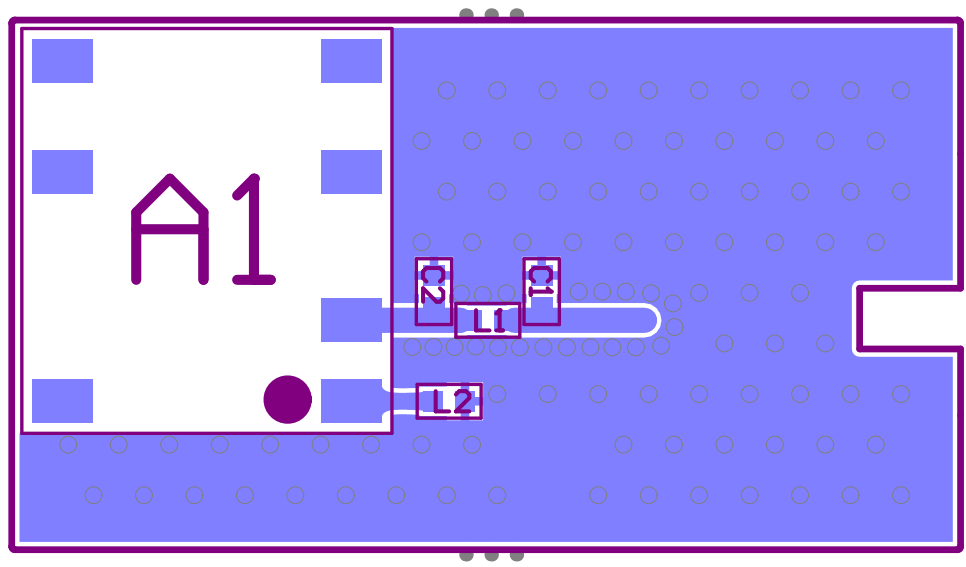
[picture p107: page 2]
